ntc-chip-revived/CHIP_Pro-Hardware/v1.0/CHIP_Pro_v1_0_Stackup.pdf

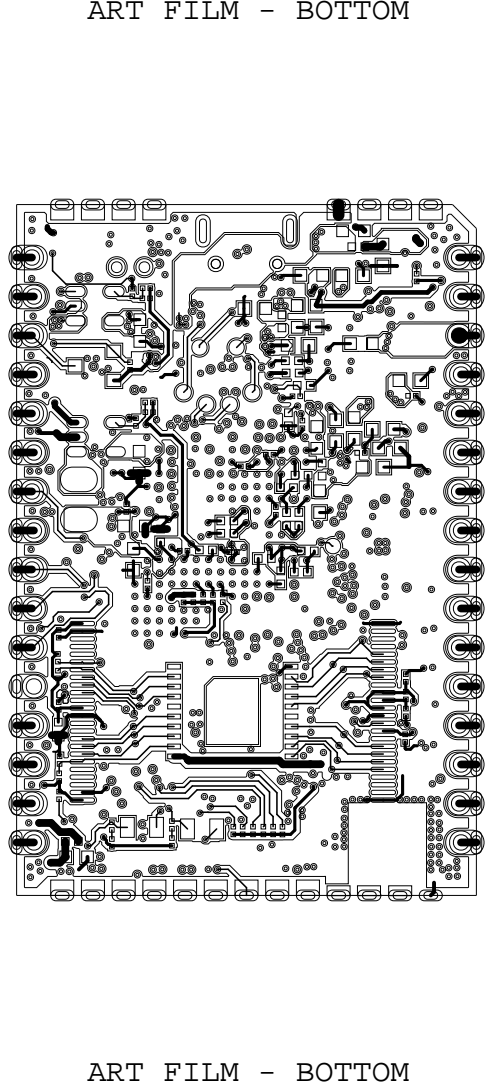
[picture p33: page 1]

ART FILM - BOTTOM

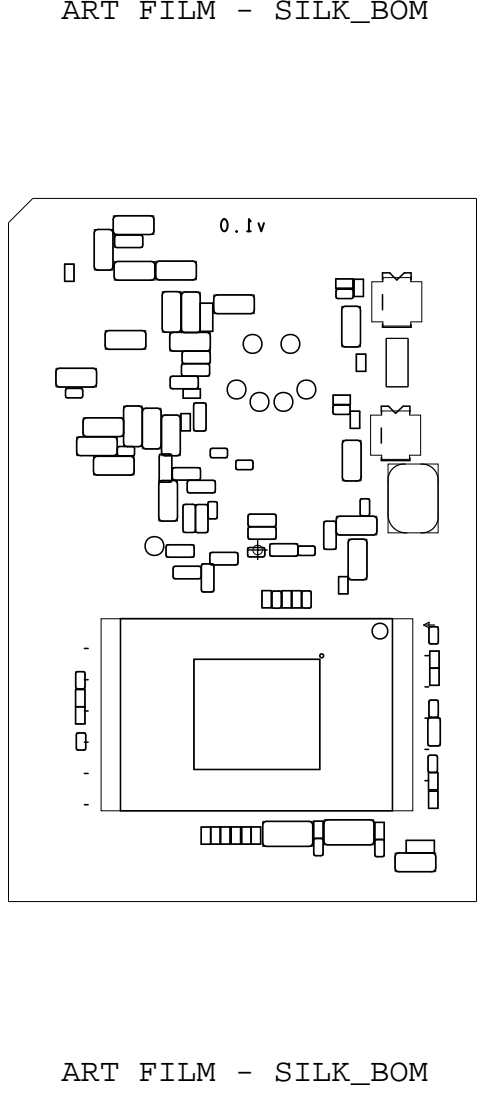
[picture p34: page 2]
ART FILM - SILK_BOM

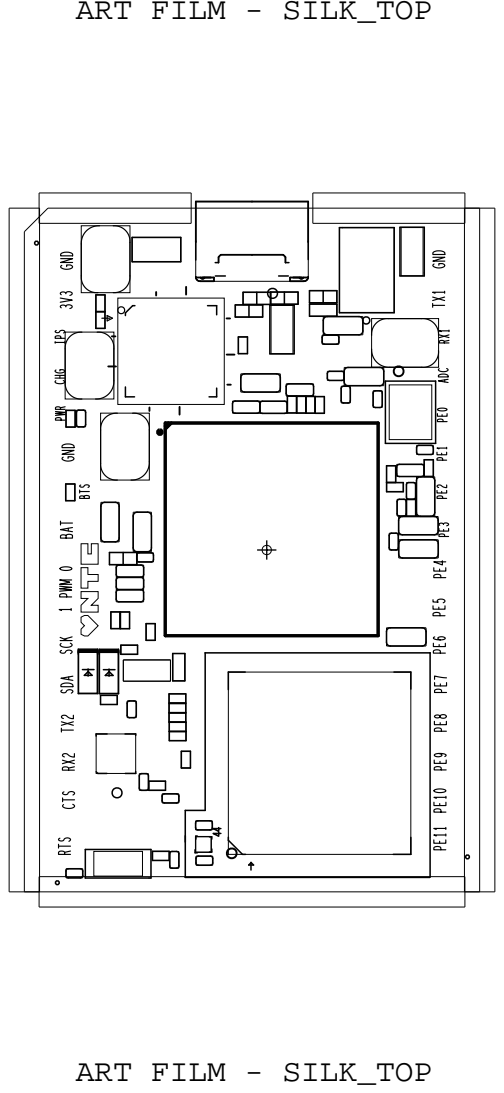
[picture p35: page 3]
ART FILM - SILK_TOP; GND TX1 ADC RX1 PE0 PE2 PE1 PE3 PE5 PE4 PE7 PE6 PE8 PE10 PE9 PE11; BTS

GND 3V3 CHG IPS PWR

GND 0 BAT 1 PWM SCK SDA TX2 CTS RX2 RTS

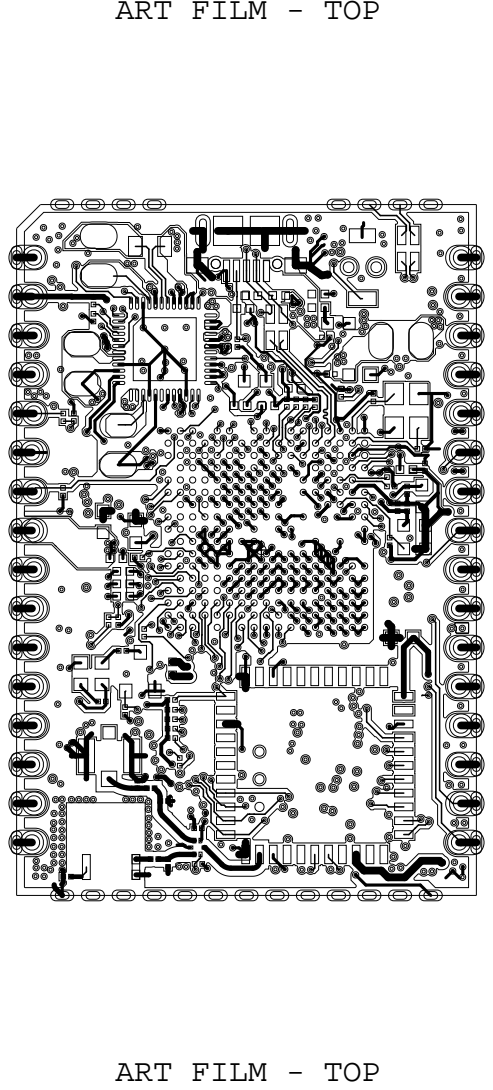
[picture p36: page 4]

ART FILM - TOP

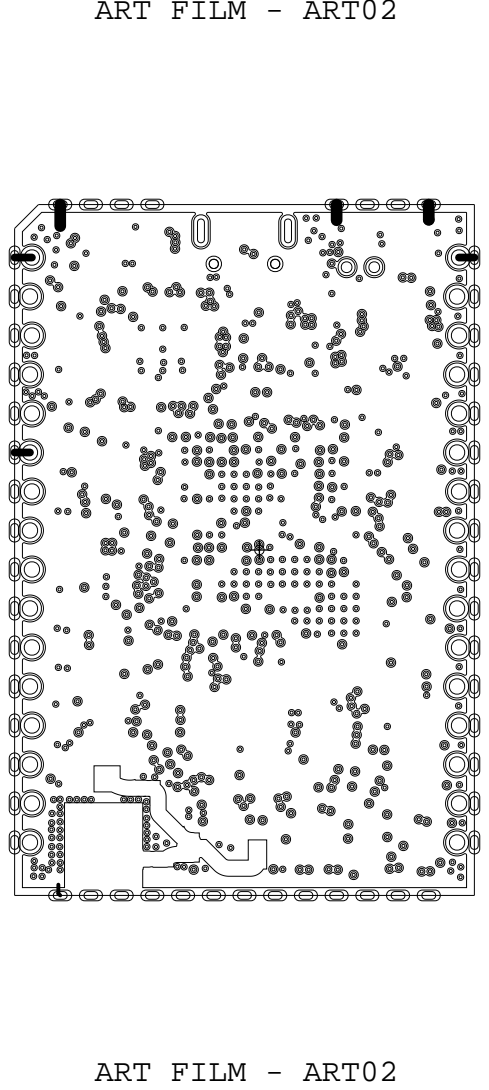
[picture p37: page 5]
ART FILM - ART02

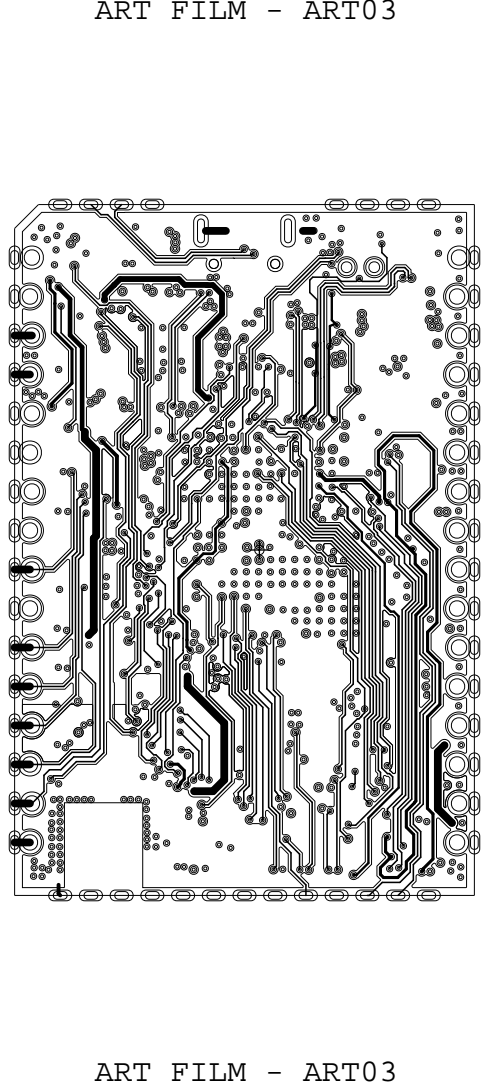
[picture p38: page 6]

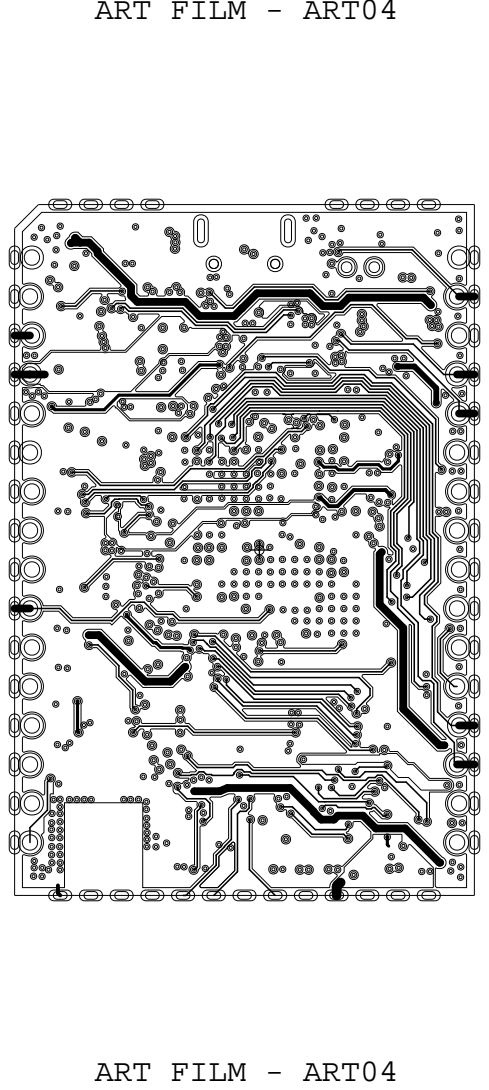
[picture p39: page 7]

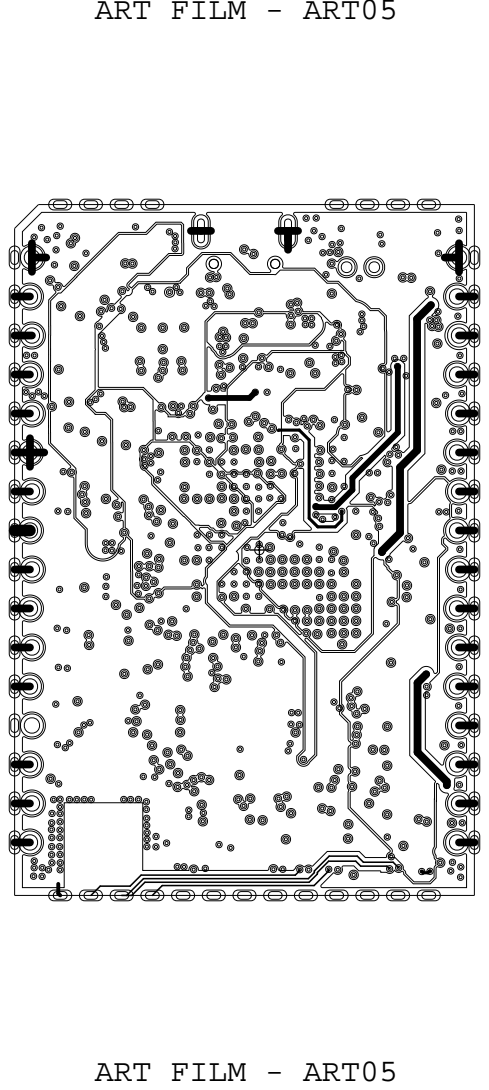
[picture p40: page 8]
