ntc-chip-revived/CHIP_Pro-Hardware/v1.0/CHIP_Pro_v1_0_PartMap.pdf

# ART FILM - ST

J5 | | J6

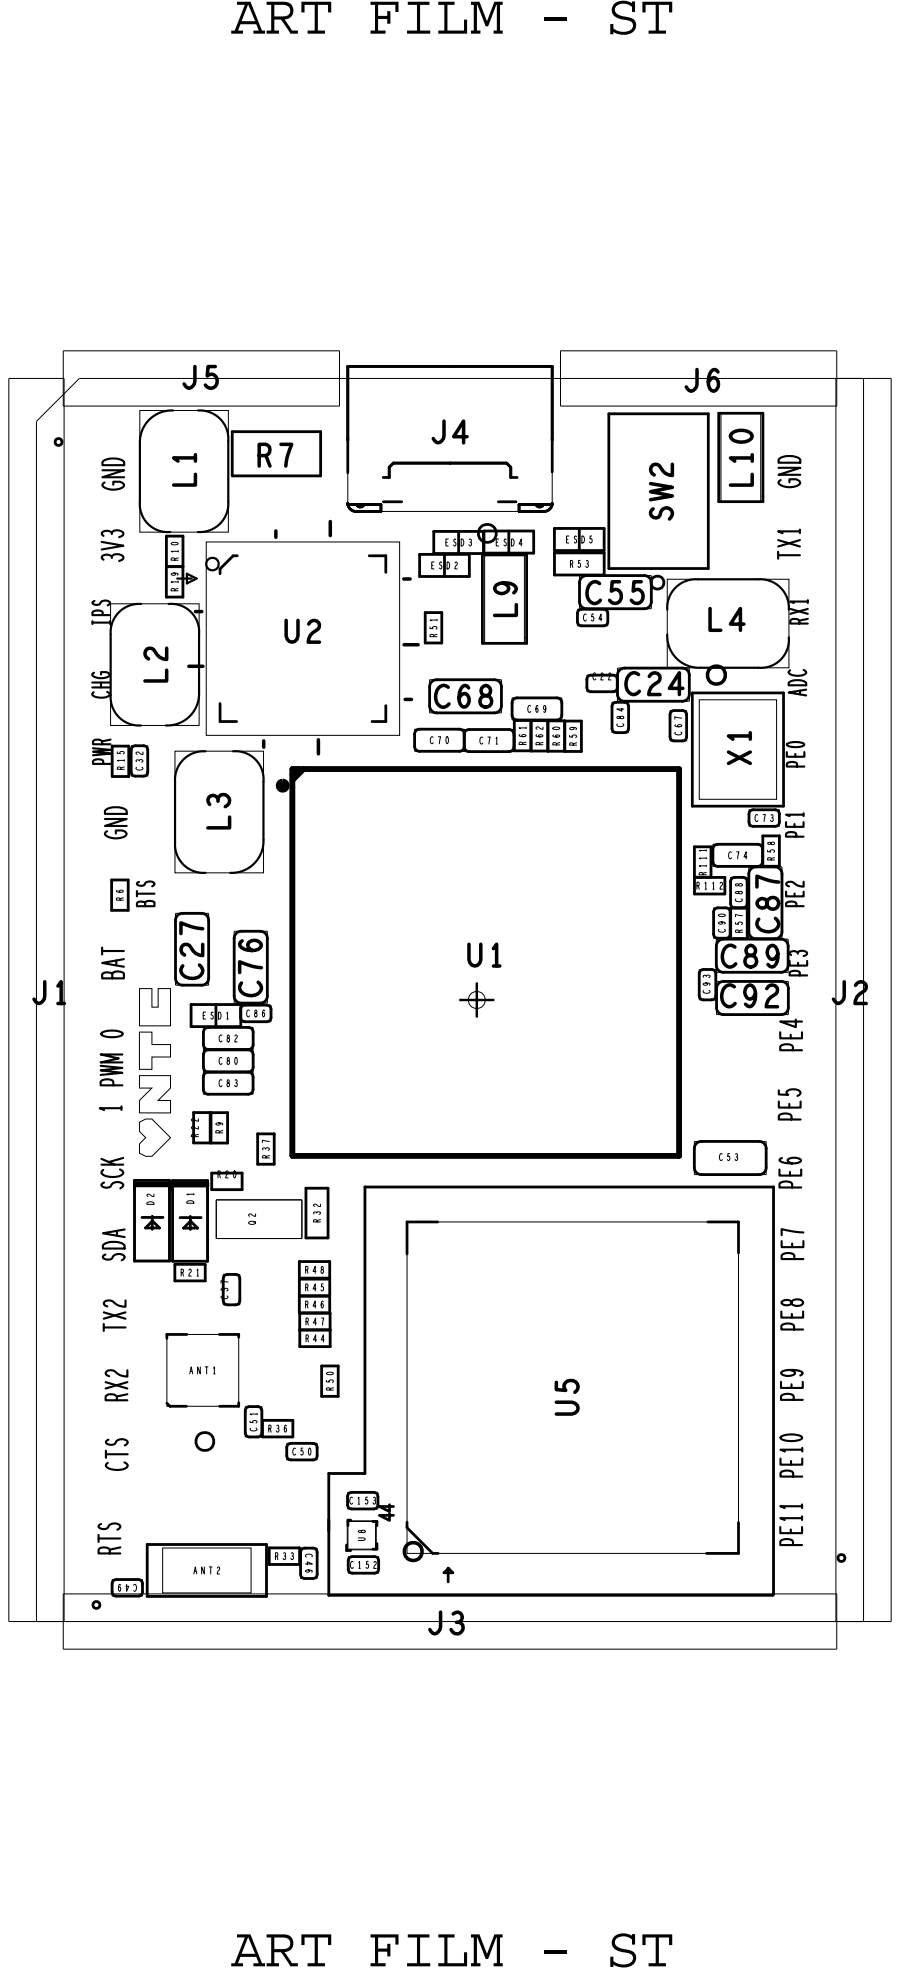
[picture p42: page 1]

# ART FILM - SB

v1.0

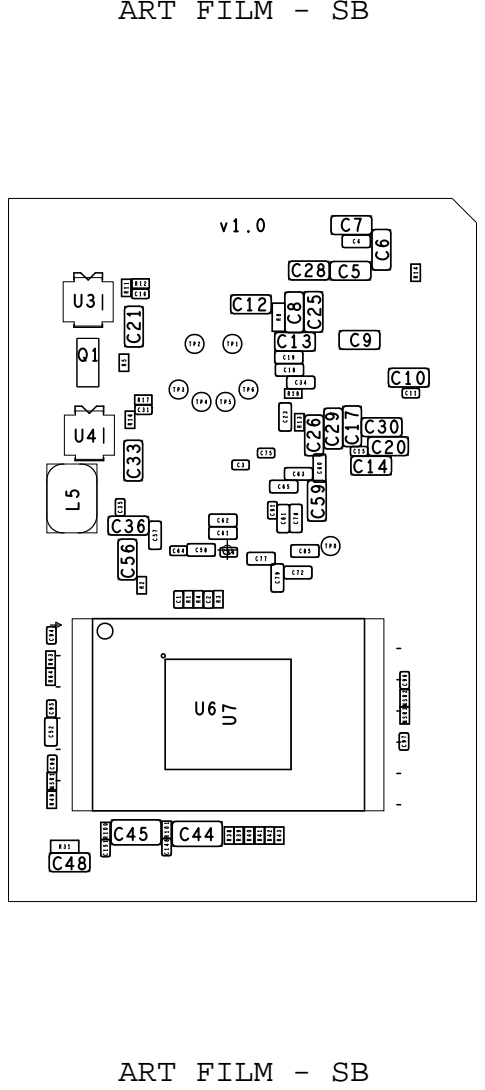
[picture p43: page 2]
