ntc-chip-revived/CHIP_Pro-Hardware/v0.9/CHIP_Pro_SCH_V0_9a.pdf

# Schematics Index：

# P01: REVISION HISTORY

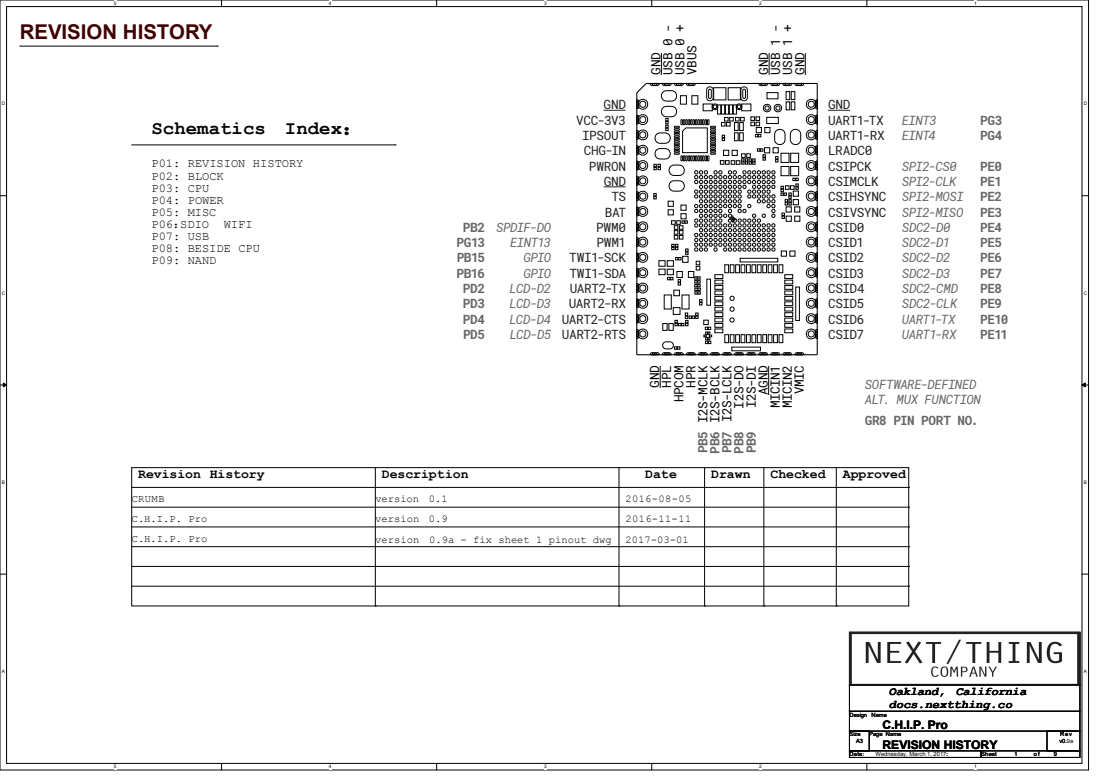
[picture p44: page 1]
Revision History; Description; Date; Drawn; Checked; Approved; P02: BLOCK P03: CPU P04: POWER P05: MISC P06：SDIO WIFI P07: USB P08: BESIDE CPU P09: NAND; REVISION HISTORY; CRUMB; version 0.1; C.H.I.P. Pro; version 0.9; Design Name; Size; Page Name; Date:; Sheet; v0.9a C.H.I.P. Pro A3; GND VCC-3V3 IPSOUT CHG-IN PWRON GND TS BAT PWM0 PWM1 TWI1-SCK TWI1-SDA UART2-TX UART2-RX UART2-CTS UART2-RTS; SPDIF-DO EINT13 GPIO GPIO LCD-D2 LCD-D3 LCD-D4 LCD-D5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

SOFTWARE-DEFINED
ALT. MUX FUNCTION
GR8 PIN PORT NO.

Oakland, California
docs.nextthing.co
C.H.I.P. Pro A3
REVISION HISTORY
Wednesday, March 1, 2017:

# BATT

# DCIN

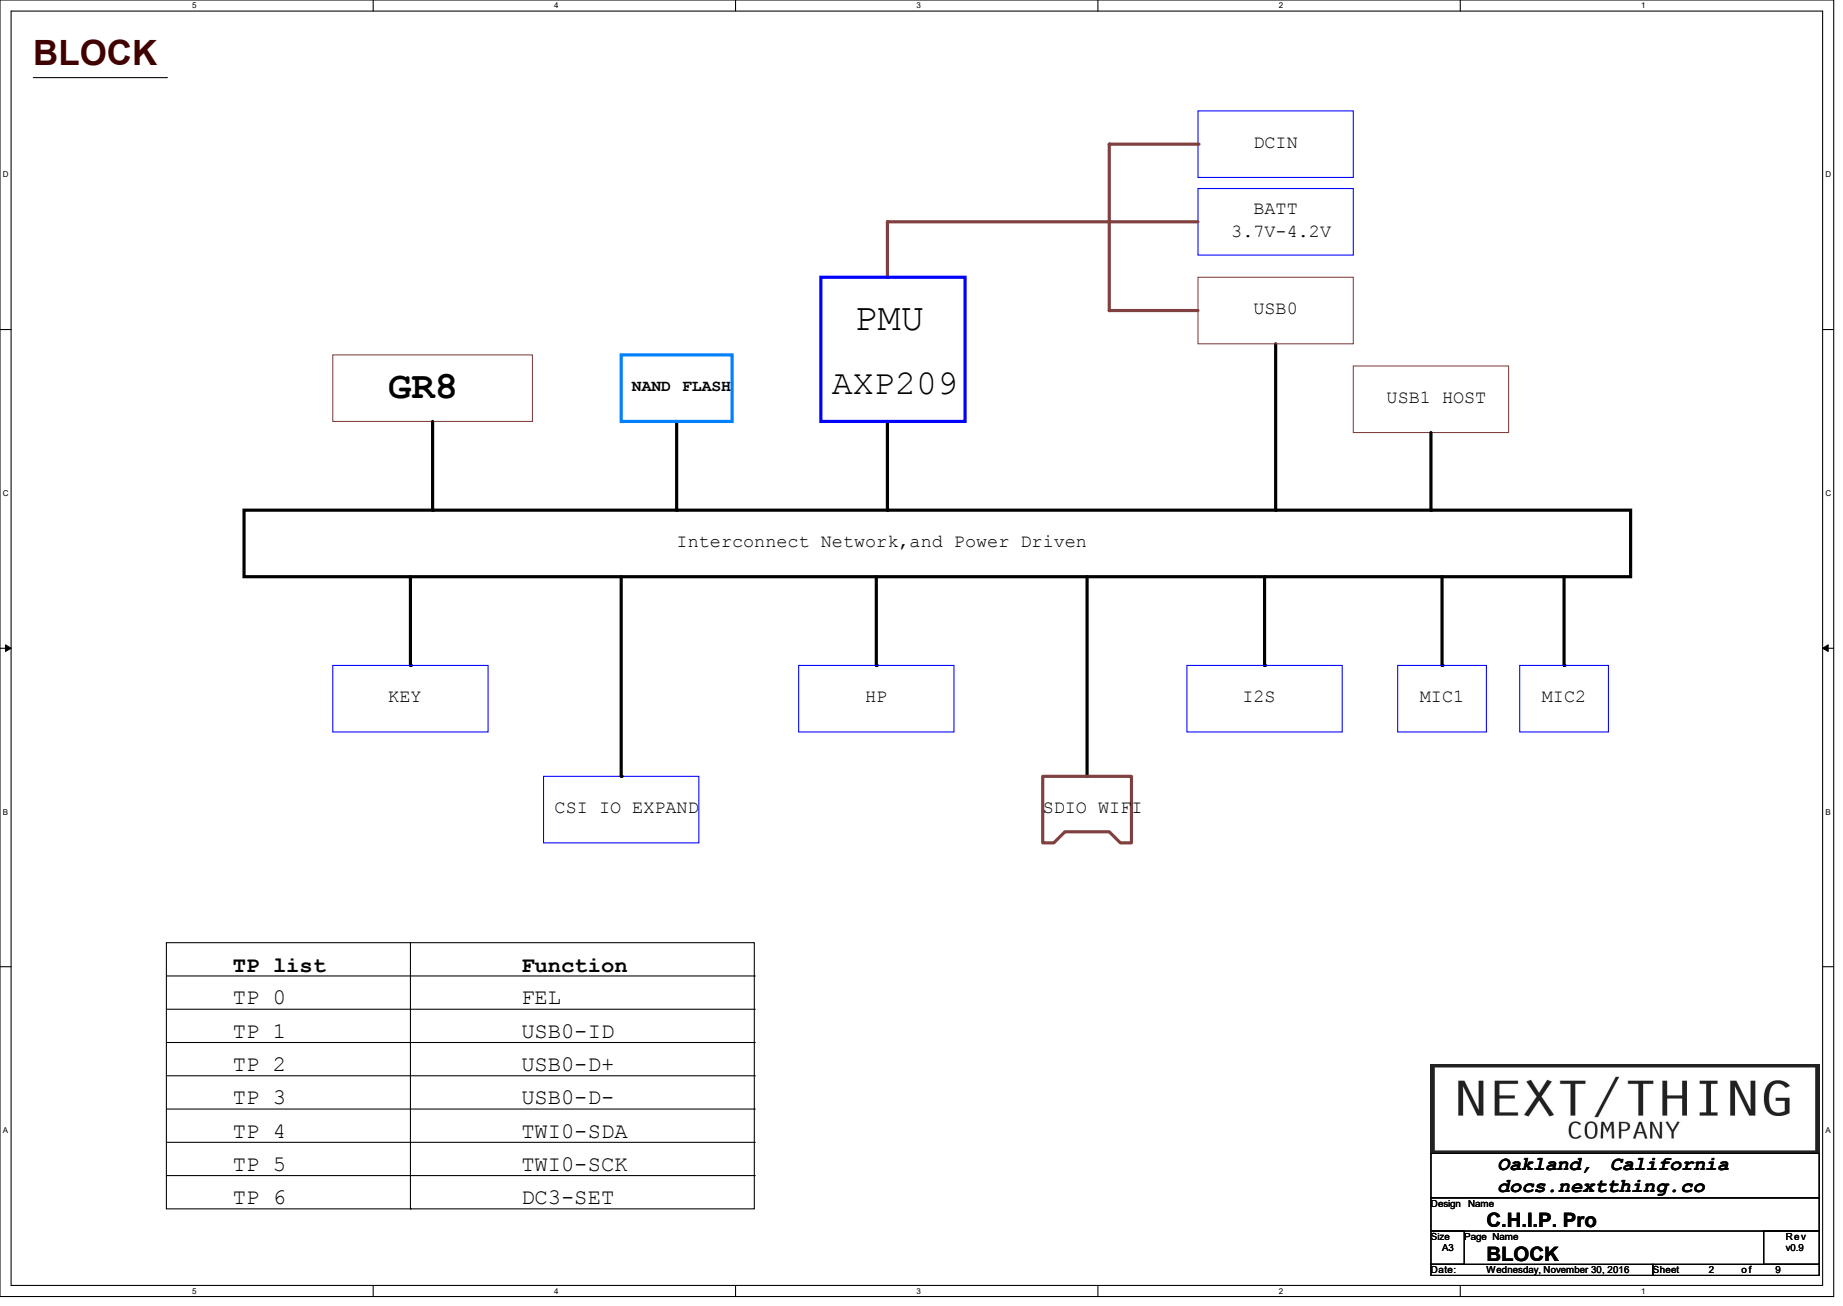
[picture p45: page 2]
SDIO WIFI; USB0; KEY; PMU; AXP209; MIC1; BLOCK; NAND FLASH GR8; USB1 HOST; MIC2; TP list; Function; FEL USB0-ID USB0-D+ USB0-D- TWI0-SDA TWI0-SCK; DC3-SET; Design Name; v0.9 C.H.I.P. Pro A3; Wednesday, November 30, 2016

Interconnect Network,and Power Driven

CSI IO EXPAND

Oakland, California
docs.nextthing.co

CPU | NAND

# SYS

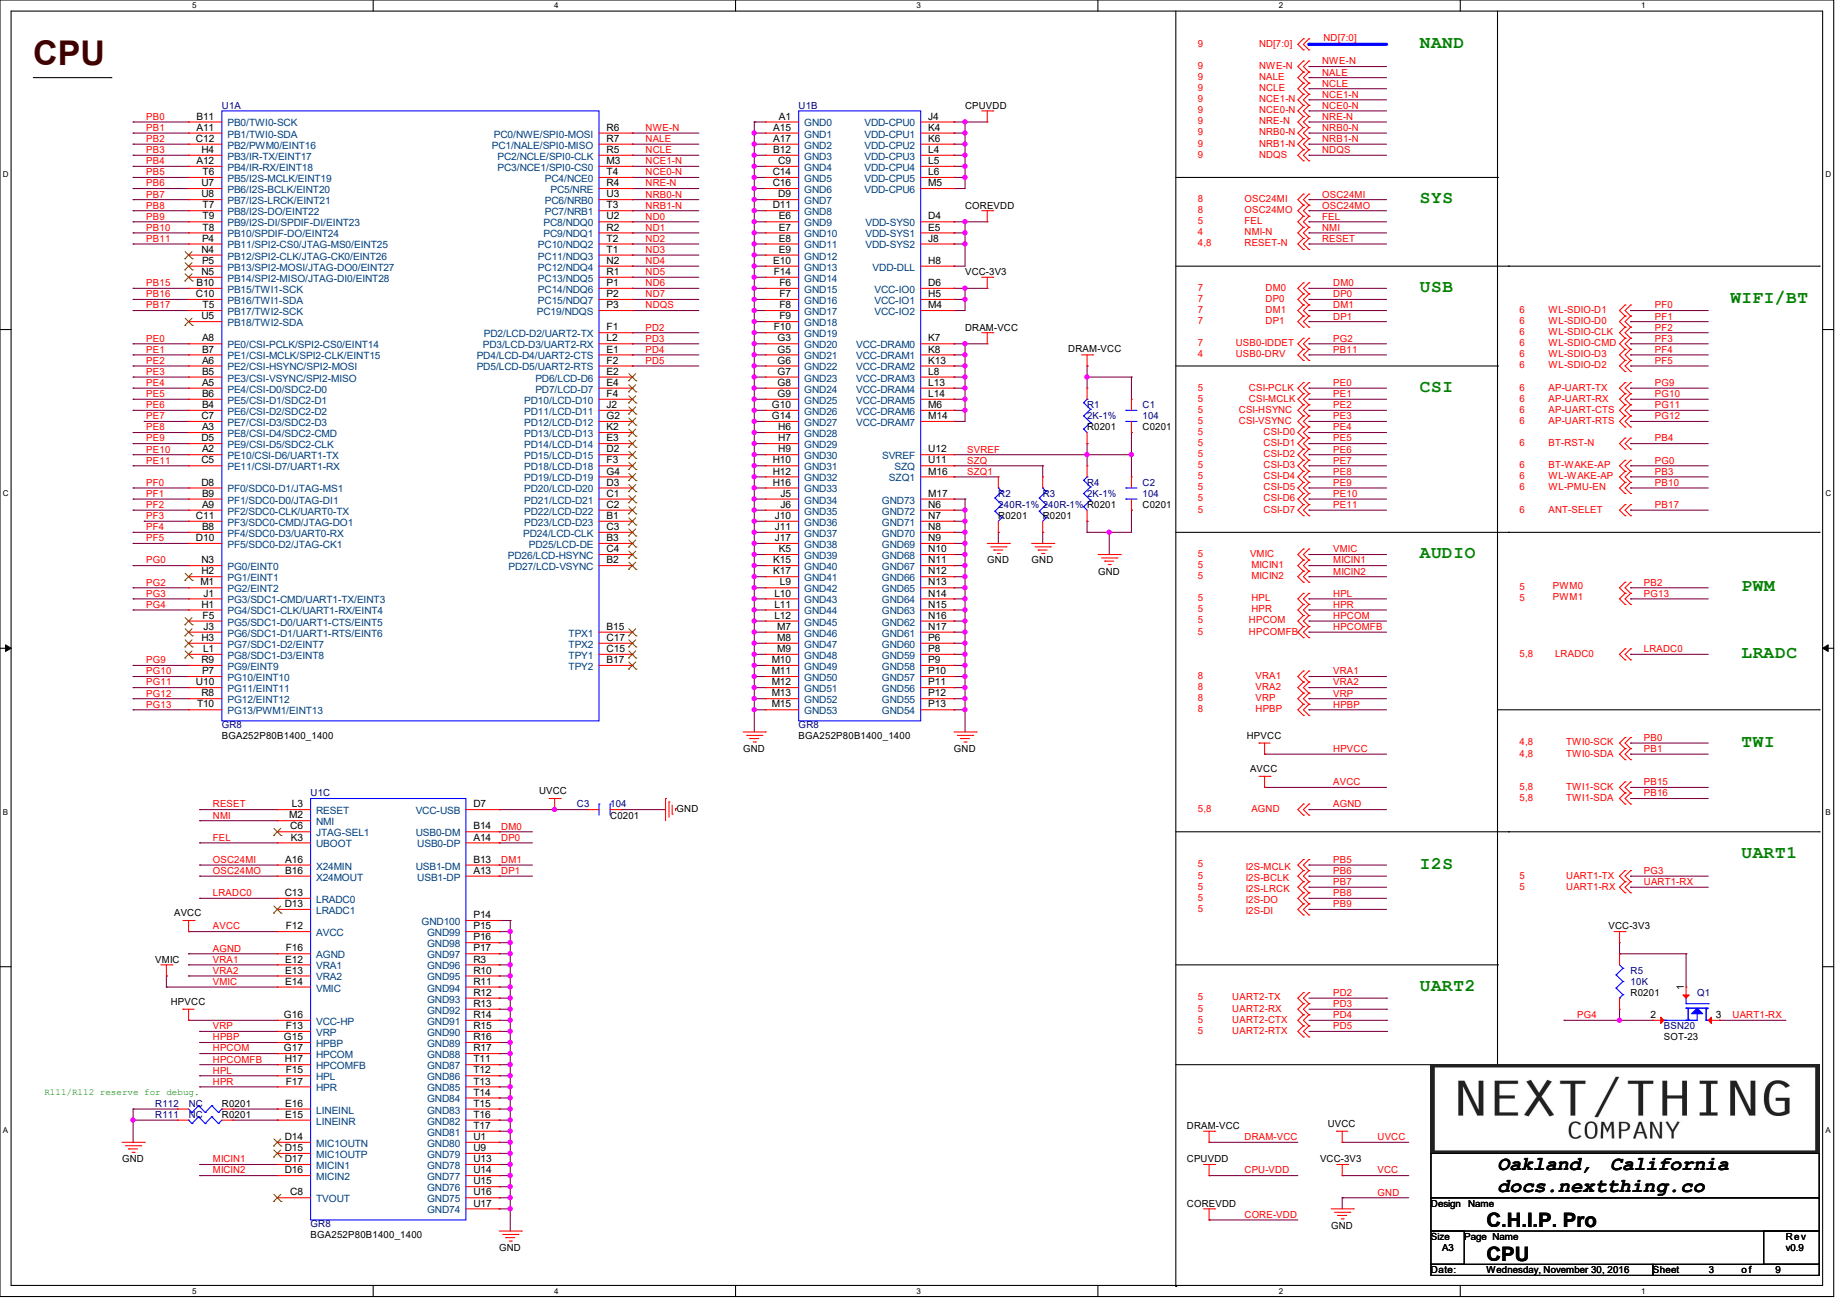
[picture p46: page 3]

VDD-CPU0 J4 VDD-CPU1 K4 VDD-CPU2 K6 VDD-CPU3 L4 VDD-CPU4 L5 VDD-CPU5 L6 VDD-CPU6 M5 VDD-DLL H8 VDD-SYS0 D4 VDD-SYS1 E5 VDD-SYS2 J8 VCC-DRAM0 K7 VCC-DRAM1 K8 VCC-DRAM2 K13 VCC-DRAM3 L8 VCC-DRAM4 L13 VCC-DRAM5 L14 VCC-DRAM6 M6 VCC-IO0 D6 VCC-IO1 H5 VCC-IO2 M4 GND25 G9 GND26 G10 GND27 G14 GND28 H6 GND29 H7 GND30 H9 GND31 H10 GND32 H12 GND33 H16
GND4 C9 GND5 C14 GND6 C16 GND7 D9 GND8 D11 GND9 E6 GND10 E7 GND11 E8 GND12 E9 GND13 E10 GND14 F14 GND15 F6 GND16 F7 GND17 F8 GND18 F9 GND44 L11 GND45 L12 GND43 L10 GND42 L9

PB0/TWI0-SCK B11 PB1/TWI0-SDA A11 PB2/PWM0/EINT16 C12 PB3/IR-TX/EINT17 H4 PB4/IR-RX/EINT18 A12 PB5/I2S-MCLK/EINT19 T6 PB6/I2S-BCLK/EINT20 U7 PB7/I2S-LRCK/EINT21 U8 PB8/I2S-DO/EINT22 T7 PB9/I2S-DI/SPDIF-DI/EINT23 T9 PB10/SPDIF-DO/EINT24 T8 PB11/SPI2-CS0/JTAG-MS0/EINT25 P4 PB12/SPI2-CLK/JTAG-CK0/EINT26 N4 PB13/SPI2-MOSI/JTAG-DO0/EINT27 P5 PB14/SPI2-MISO/JTAG-DI0/EINT28 N5 PB15/TWI1-SCK B10 PB16/TWI1-SDA C10 PB17/TWI2-SCK T5 PB18/TWI2-SDA U5 PE0/CSI-PCLK/SPI2-CS0/EINT14 A8 PE1/CSI-MCLK/SPI2-CLK/EINT15 B7 PE2/CSI-HSYNC/SPI2-MOSI A6 PE3/CSI-VSYNC/SPI2-MISO B5 PE4/CSI-D0/SDC2-D0 A5 PE5/CSI-D1/SDC2-D1 B6 PE6/CSI-D2/SDC2-D2 B4 PE7/CSI-D3/SDC2-D3 C7 PE8/CSI-D4/SDC2-CMD A3 PE9/CSI-D5/SDC2-CLK D5 PE10/CSI-D6/UART1-TX A2 PE11/CSI-D7/UART1-RX C5 PF0/SDC0-D1/JTAG-MS1 D8 PF1/SDC0-D0/JTAG-DI1 B9 PF2/SDC0-CLK/UART0-TX A9 PF3/SDC0-CMD/JTAG-DO1 C11 PF4/SDC0-D3/UART0-RX B8 PF5/SDC0-D2/JTAG-CK1 D10 PG0/EINT0 N3 PG1/EINT1 H2 PG2/EINT2 M1 PG3/SDC1-CMD/UART1-TX/EINT3 J1 PG4/SDC1-CLK/UART1-RX/EINT4 H1 PG5/SDC1-D0/UART1-CTS/EINT5 F5 PG6/SDC1-D1/UART1-RTS/EINT6 J3 PG7/SDC1-D2/EINT7 H3 PG8/SDC1-D3/EINT8 L1 PG9/EINT9 R9 PG10/EINT10 P7 PG11/EINT11 U10 PG12/EINT12 R8 PG13/PWM1/EINT13 T10

PC1/NALE/SPI0-MISO R7 PC0/NWE/SPI0-MOSI R6 PC3/NCE1/SPI0-CS0 M3 PC2/NCLE/SPI0-CLK R5 PC5/NRE R4 PC6/NRB0 U3 PC8/NDQ0 U2 PC10/NDQ2 T2 PC11/NDQ3 T1 PC13/NDQ5 R1 PC12/NDQ4 N2 PC19/NDQS P3 PC14/NDQ6 P1 PC9/NDQ1 R2 PC7/NRB1 T3 PC4/NCE0 T4 PC15/NDQ7 P2

PD2/LCD-D2/UART2-TX F1 PD3/LCD-D3/UART2-RX L2 PD4/LCD-D4/UART2-CTS E1 PD5/LCD-D5/UART2-RTS F2 PD6/LCD-D6 E2 PD7/LCD-D7 E4 PD10/LCD-D10 F4 PD11/LCD-D11 J2 PD12/LCD-D12 G2 PD13/LCD-D13 K2 PD14/LCD-D14 E3 PD15/LCD-D15 D2 PD18/LCD-D18 F3 PD19/LCD-D19 G4 PD20/LCD-D20 D3 PD21/LCD-D21 C1 PD22/LCD-D22 C2 PD23/LCD-D23 B1 PD24/LCD-CLK C3 PD25/LCD-DE B3 PD26/LCD-HSYNC C4 PD27/LCD-VSYNC B2

HPBP HPL NMI RESET OSC24MI OSC24MO

VCC-USB D7 USB0-DM B14 USB0-DP A14 USB1-DM B13 USB1-DP A13 HPBP G15

# POWER/PMU

# VCC-1V8 AVCC

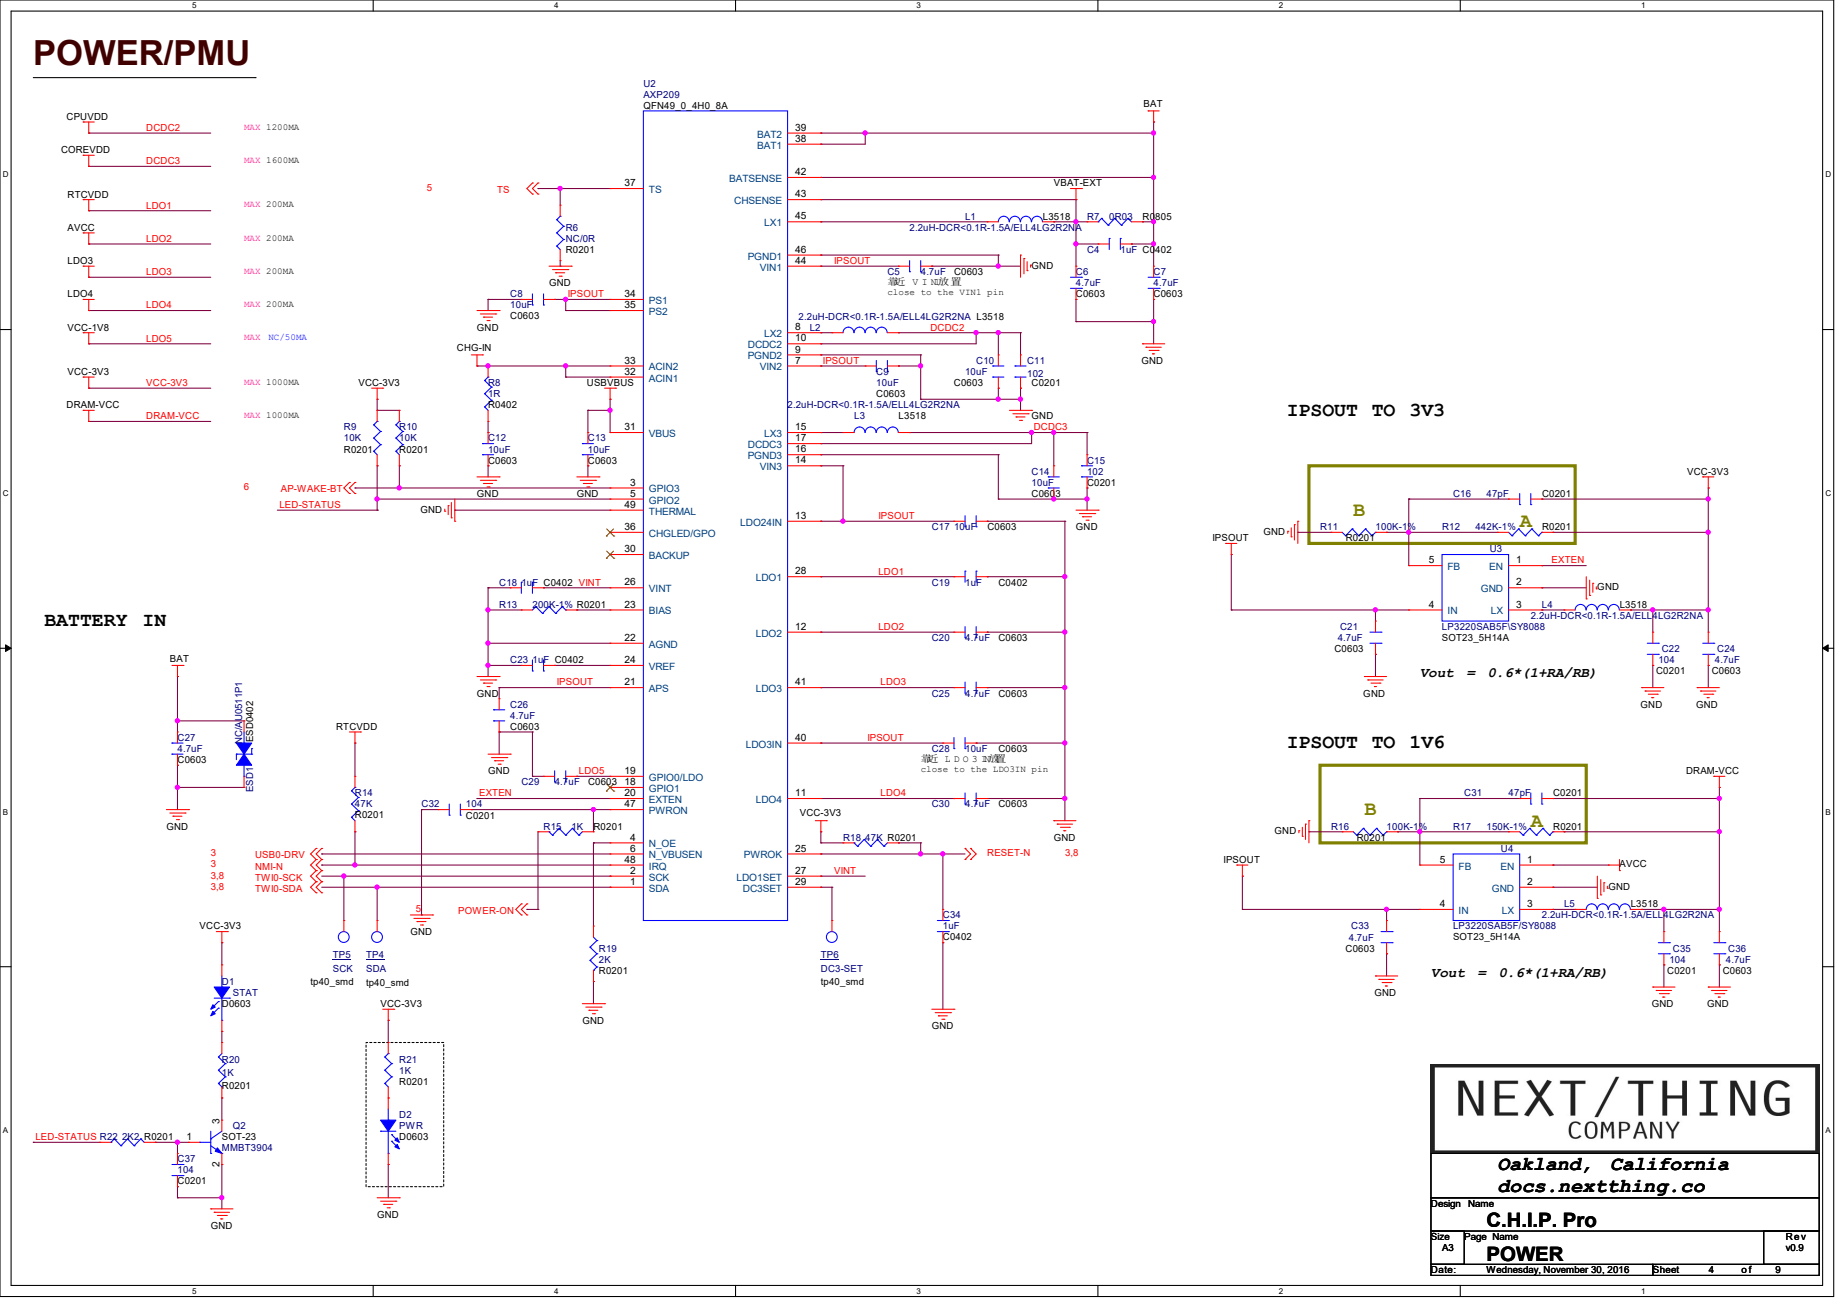
[picture p47: page 4]

BATSENSE 42 CHSENSE 43 VIN1 44
BACKUP 30 VBUS 31 ACIN1 32 ACIN2 33 PS1 34 PS2 35 CHGLED/GPO 36

close to the VIN1 pin

靠近 L D O 3 IN放置
close to the LDO3IN pin

# MISC

# PWM0 TSUART2-RTX UART2-TX

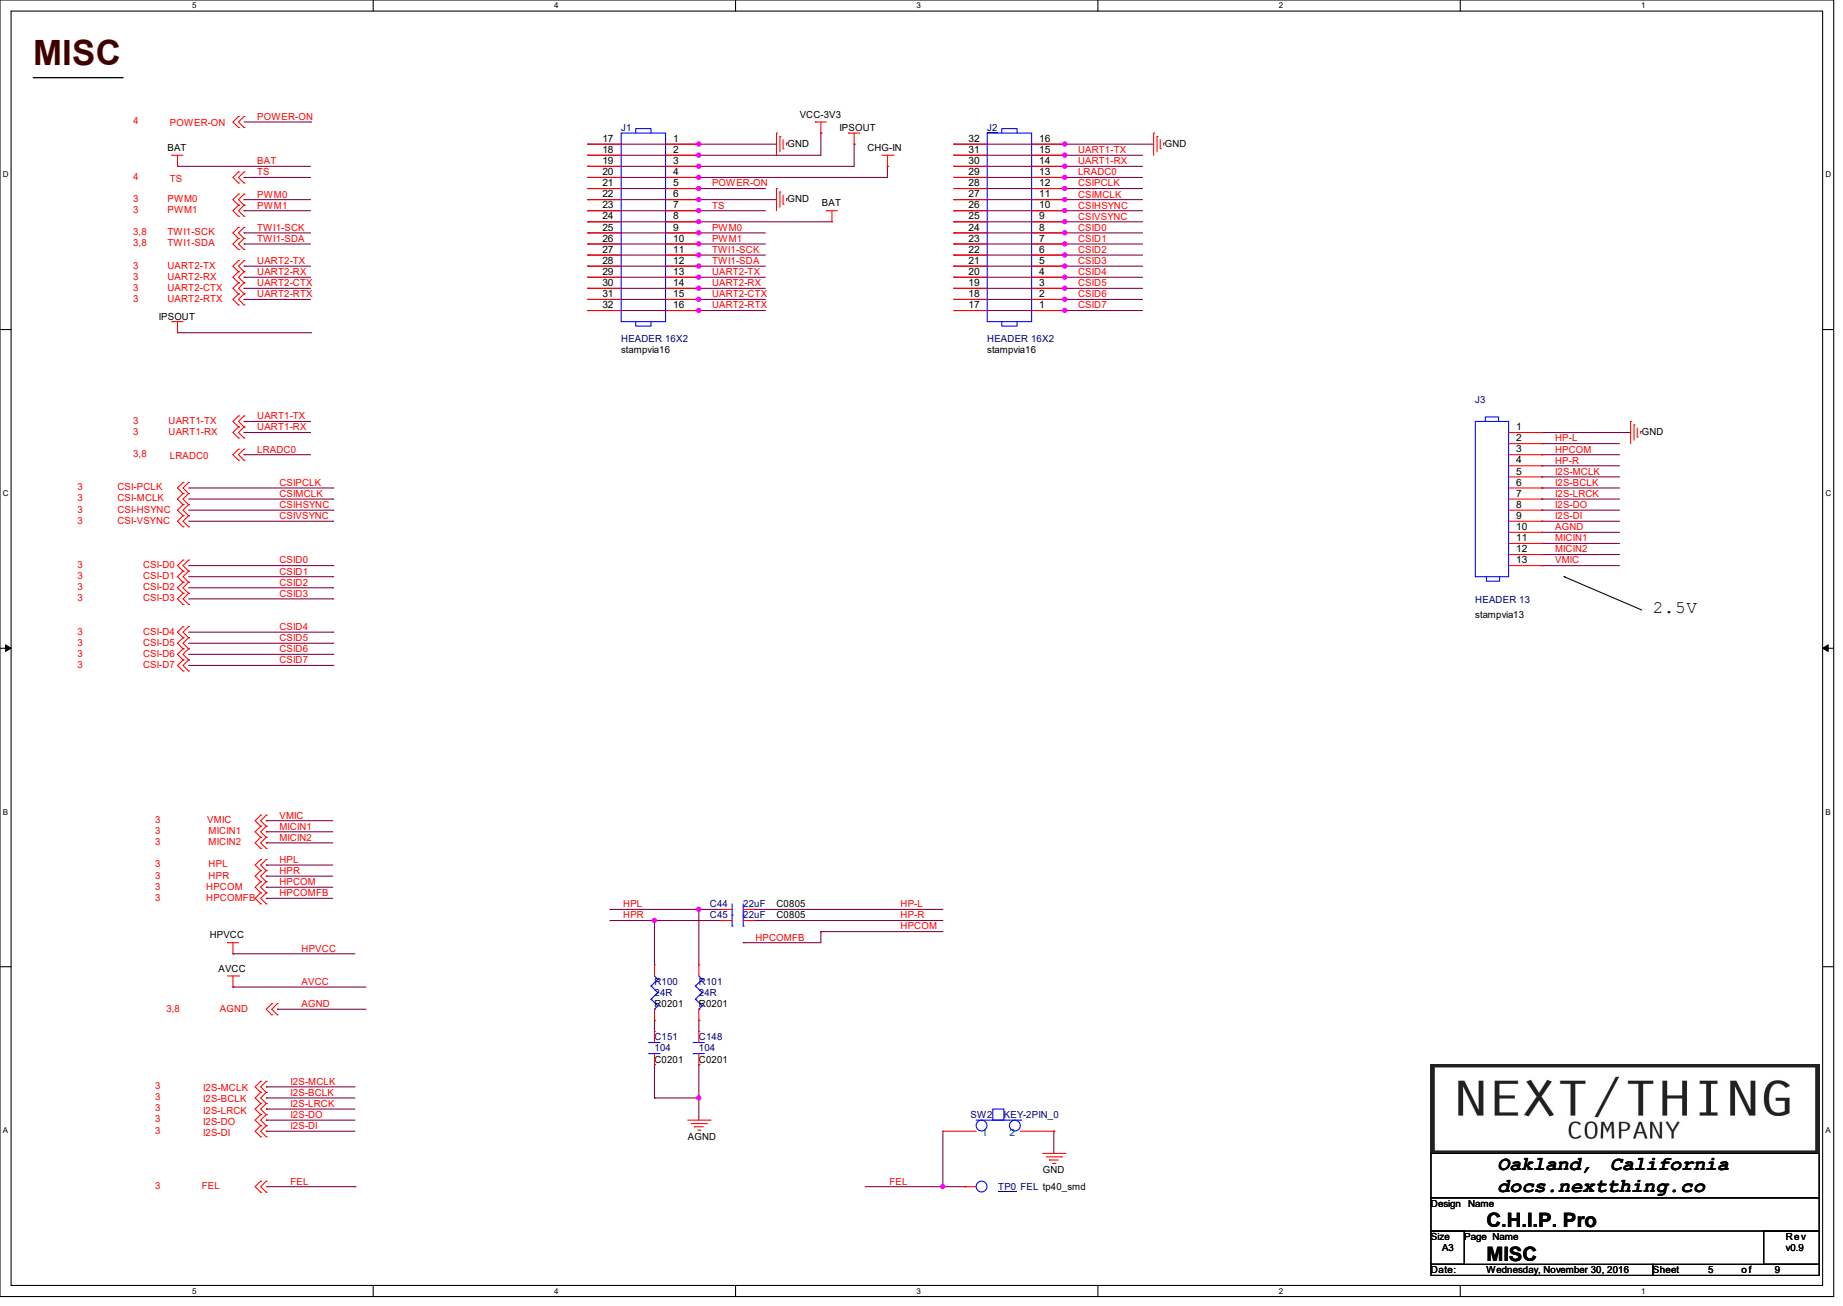
[picture p48: page 5]

IPSOUT GND BAT GND

TWI1-SCK
TWI1-SDA UART2-RTX UART2-CTX UART2-RX UART2-TX

A

B

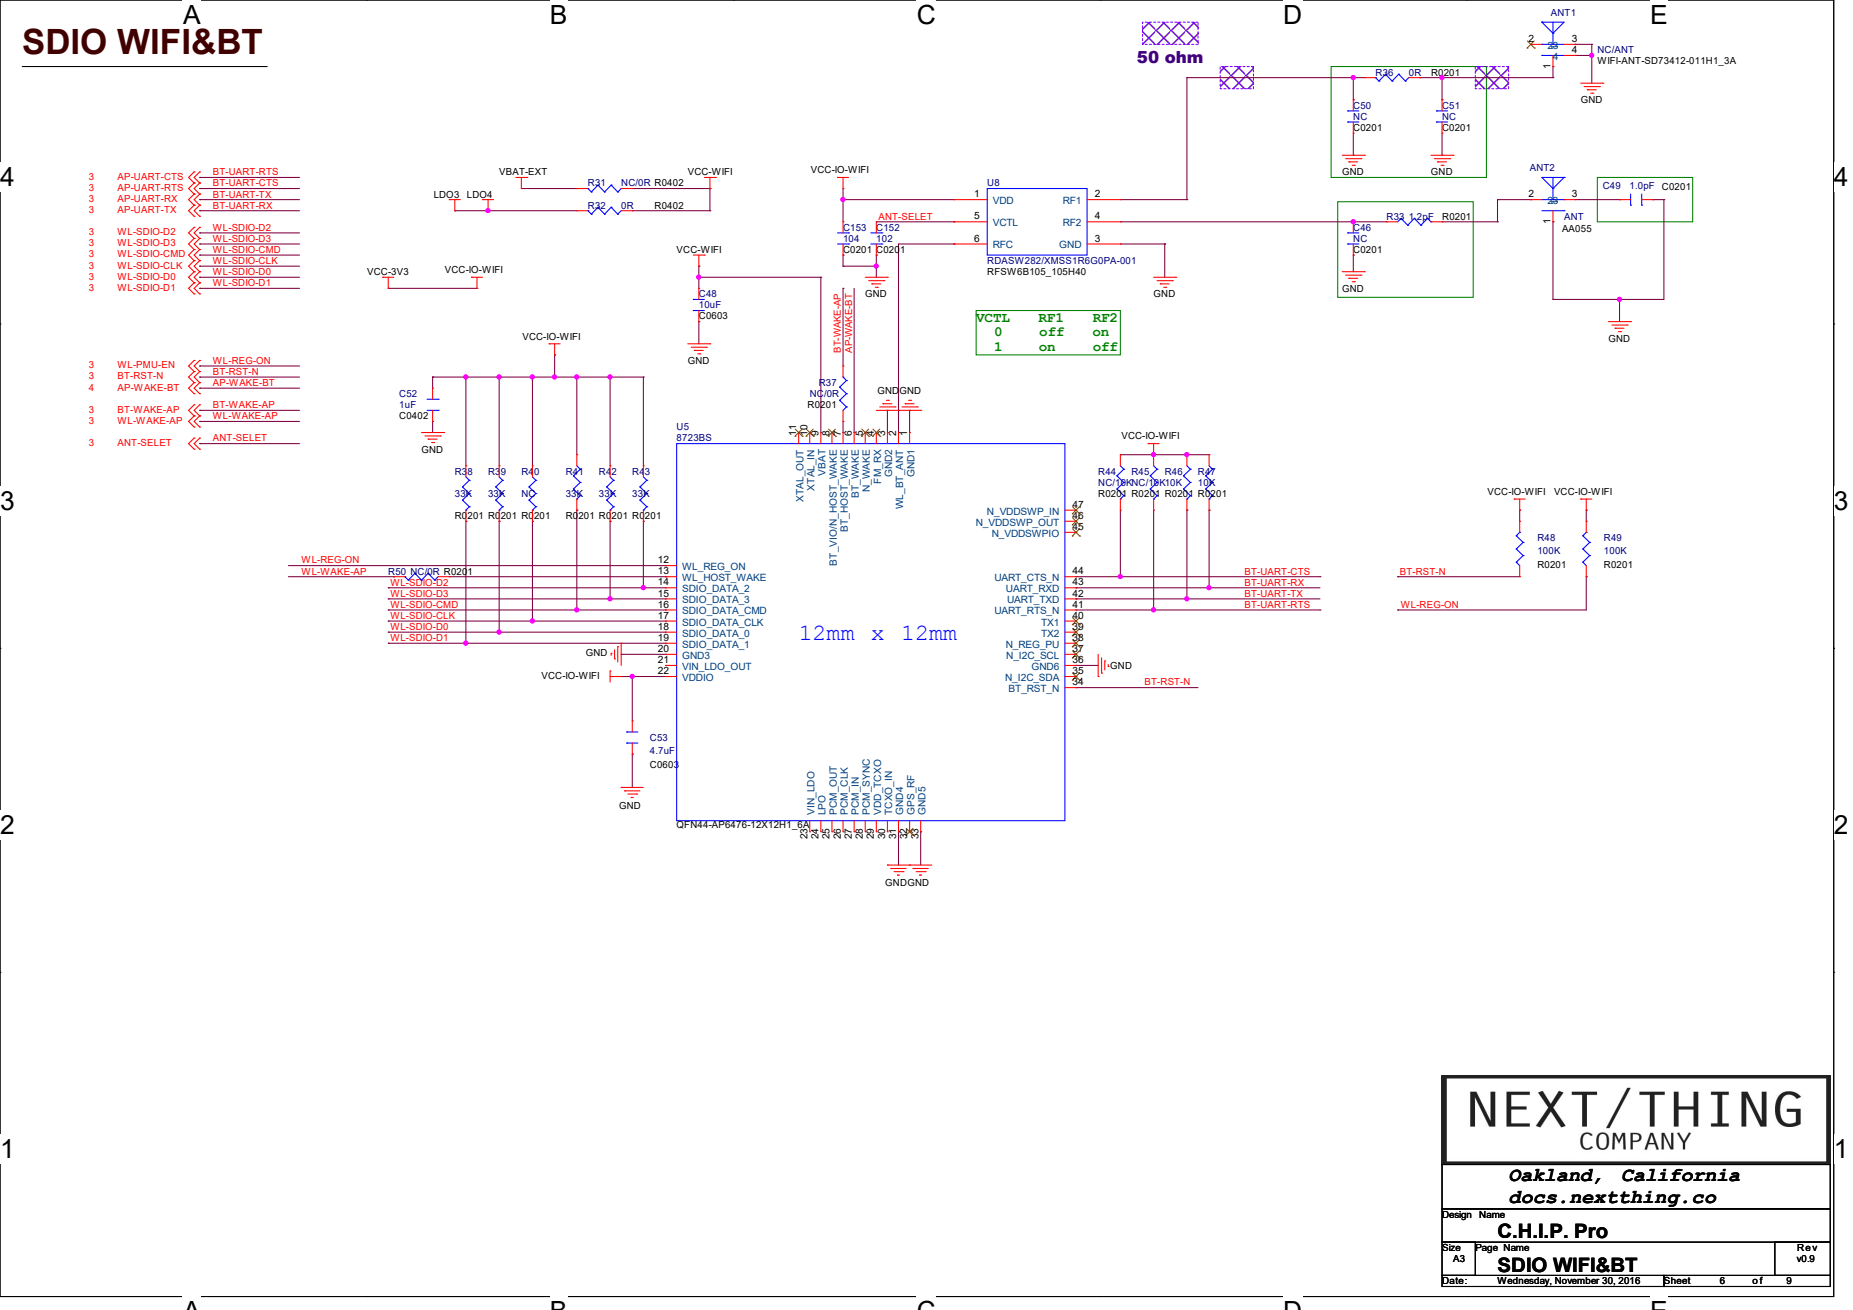
[picture p49: page 6]

BT-UART-RTS
BT-UART-CTS
BT-UART-TX
AP-WAKE-BT BT-RST-N WL-SDIO-D2 WL-SDIO-D3 WL-SDIO-CMD WL-SDIO-CLK WL-SDIO-D0 WL-SDIO-D1 BT-UART-RX

BT-RST-N WL-REG-ON WL-REG-ON

BT-RST-N WL-SDIO-CLK

# USB

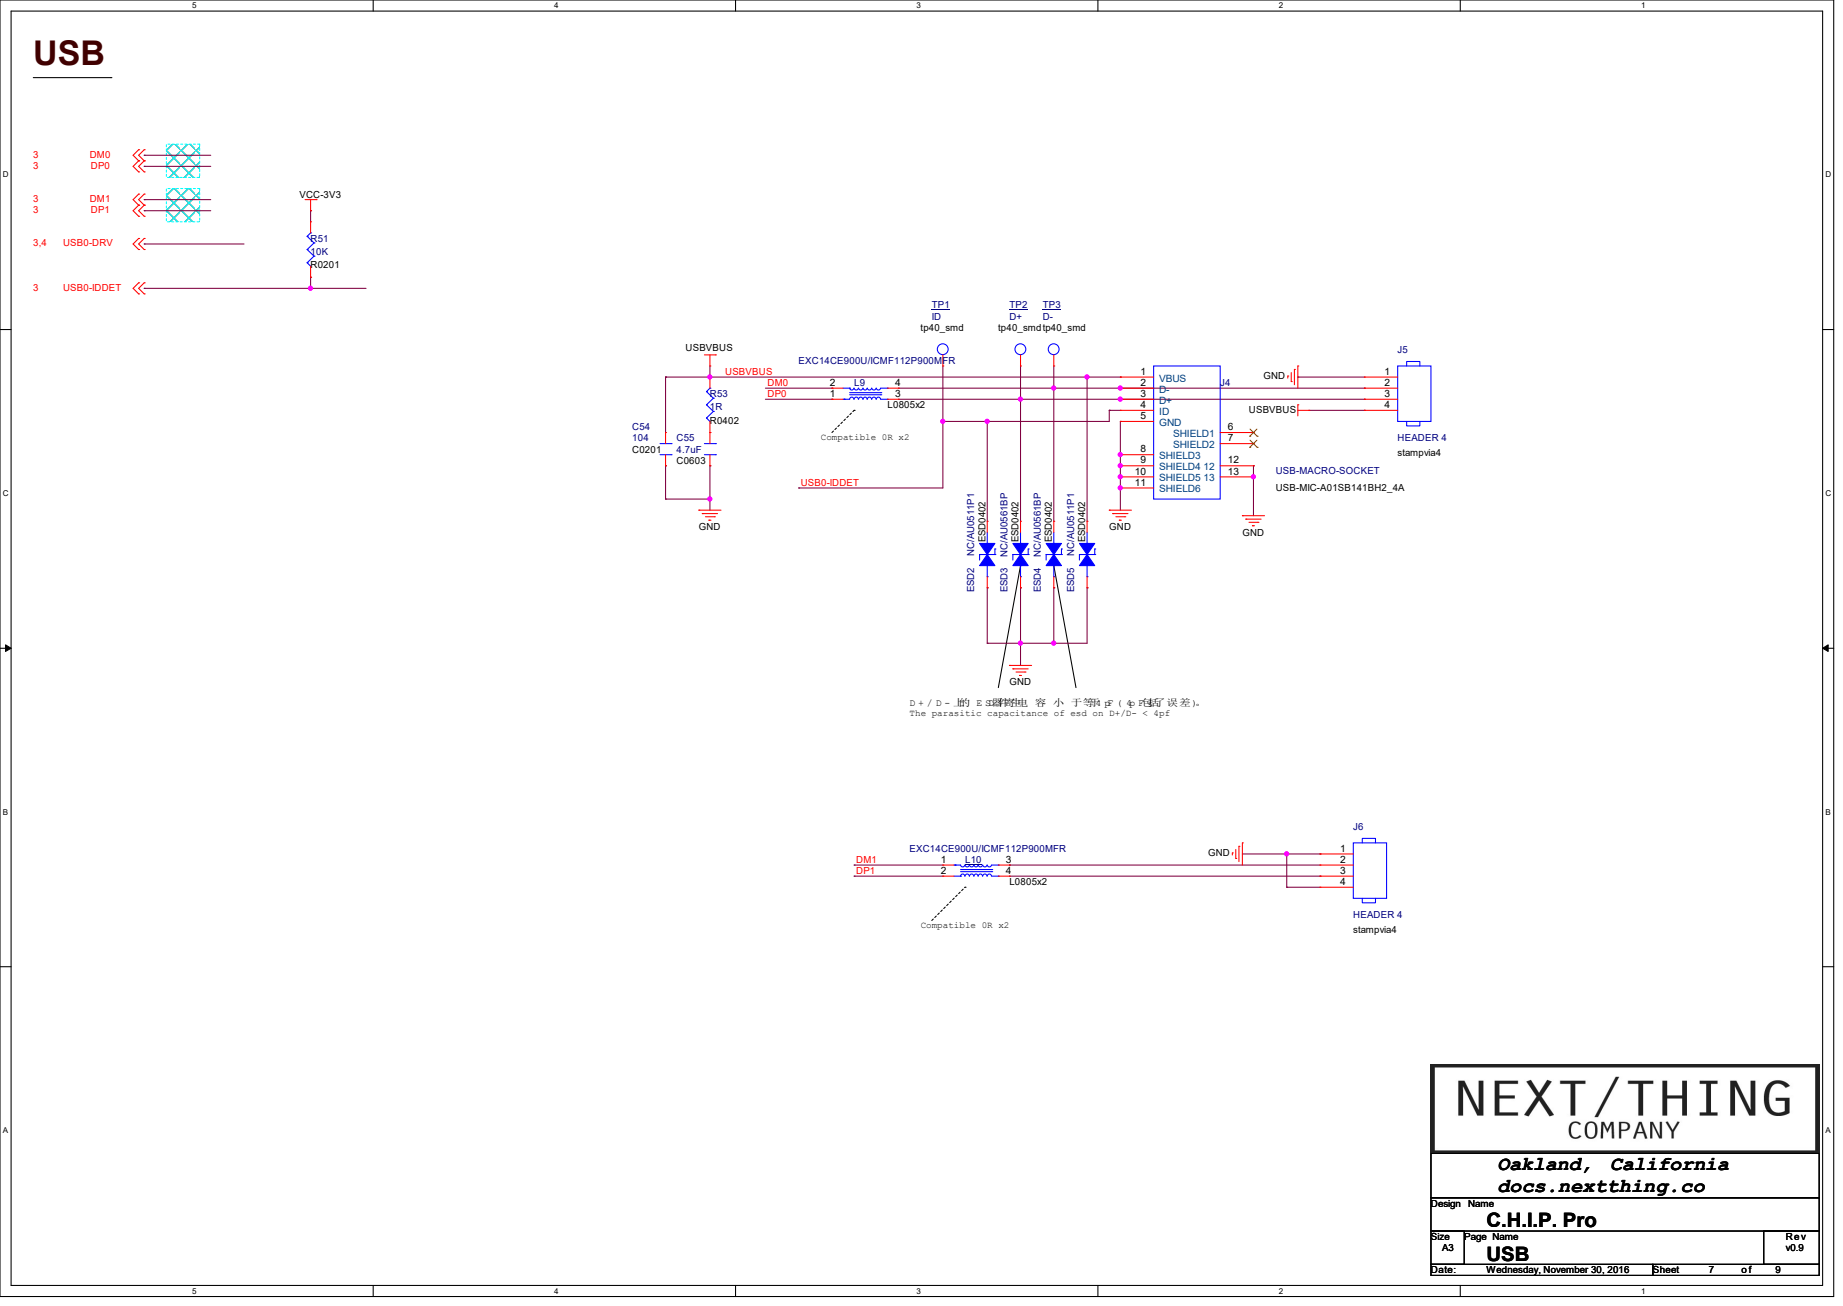
[picture p50: page 7]

4 ESD⁴ NC/AU⁰⁵⁶¹BP ESD⁰⁴⁰² TP2 D+

4 ESD³ NC/AU⁰⁵⁶¹BP ESD⁰⁴⁰²

D + / D - 上的 E SD器件寄生电 容 小 于等于4 pF ( 4p F包括了误差)。
The parasitic capacitance of esd on D+/D- < 4pf

# DRAM

# PIO-INTFACE

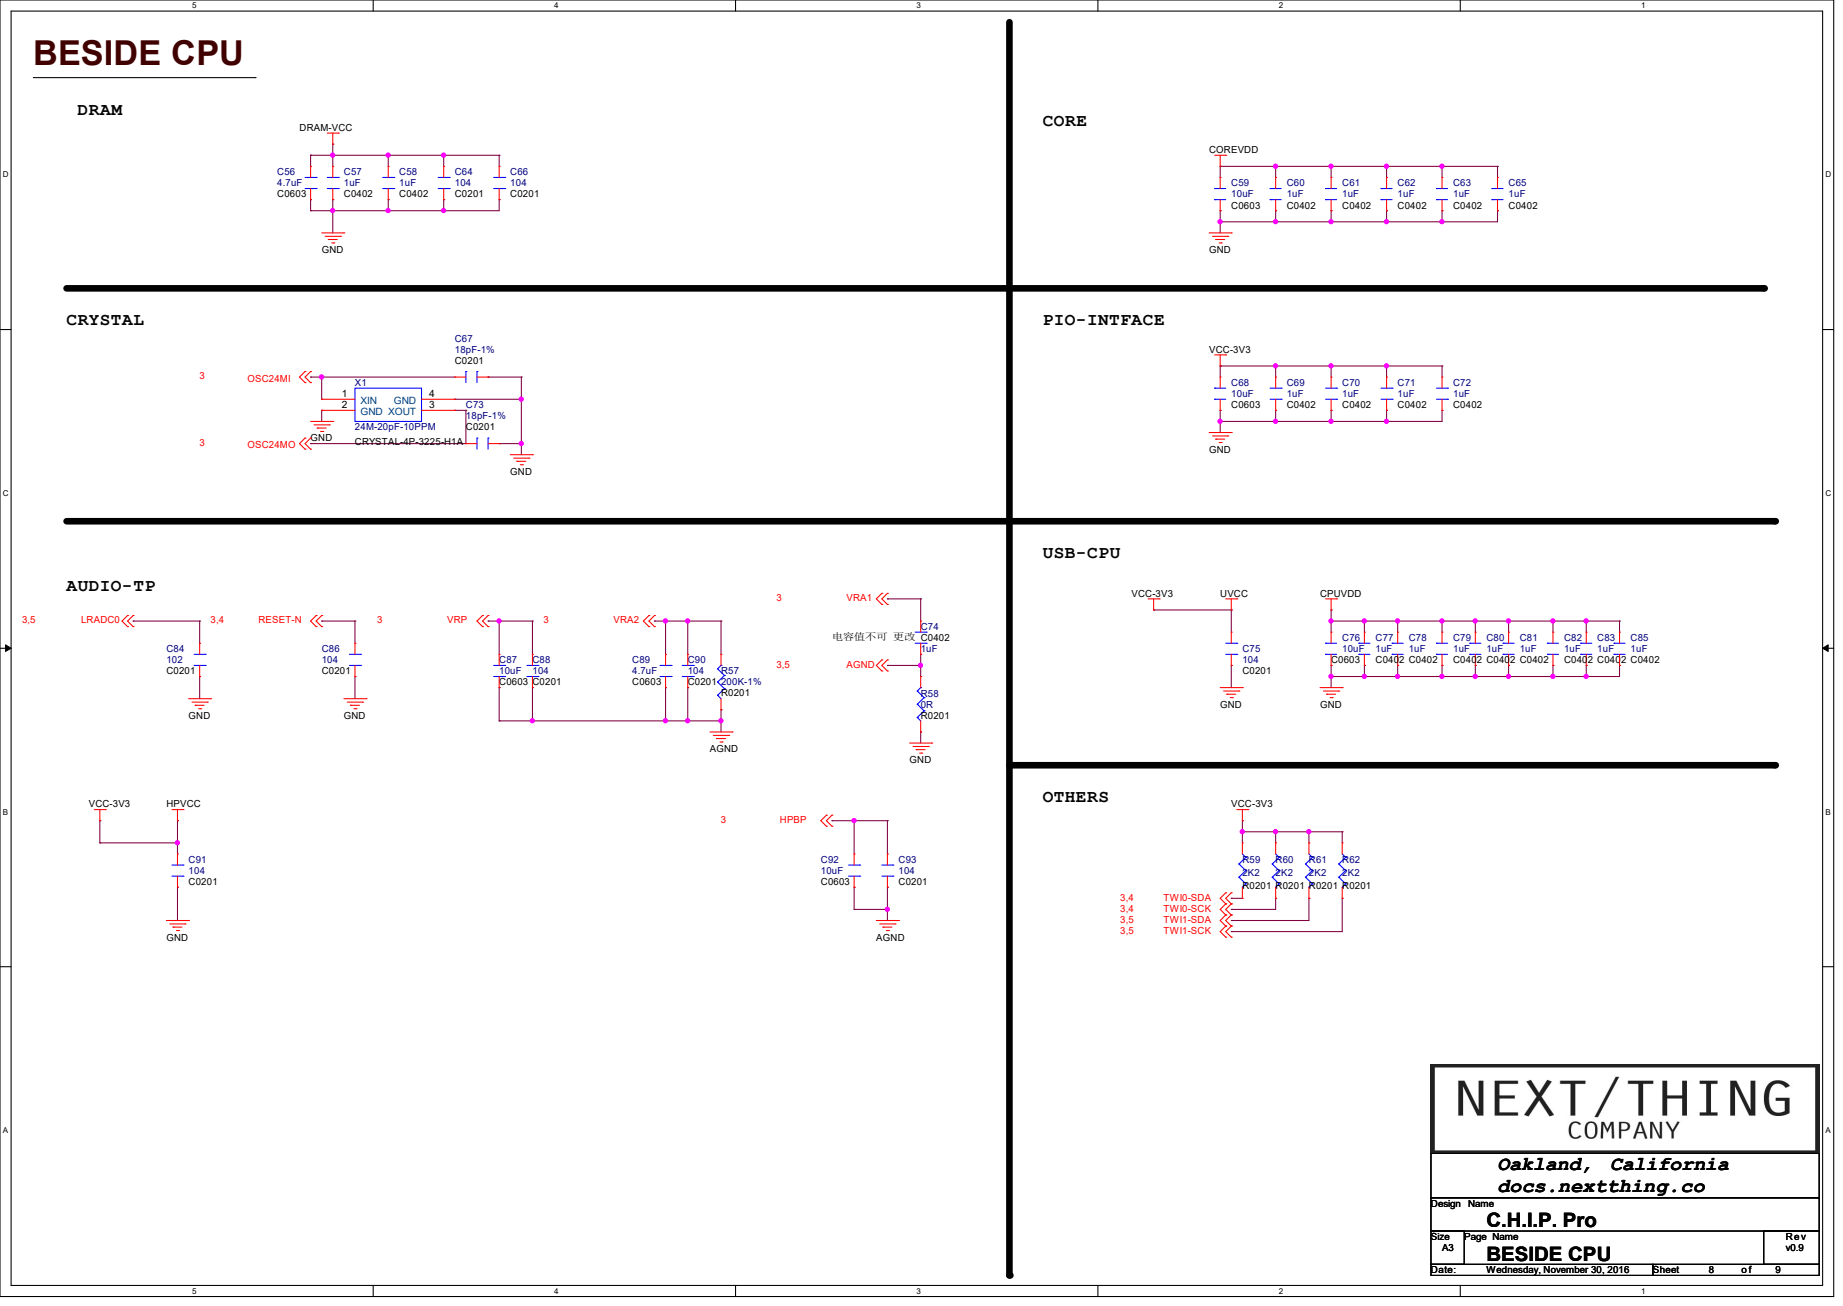
[picture p51: page 8]

# NAND

# NALE NRB1-N

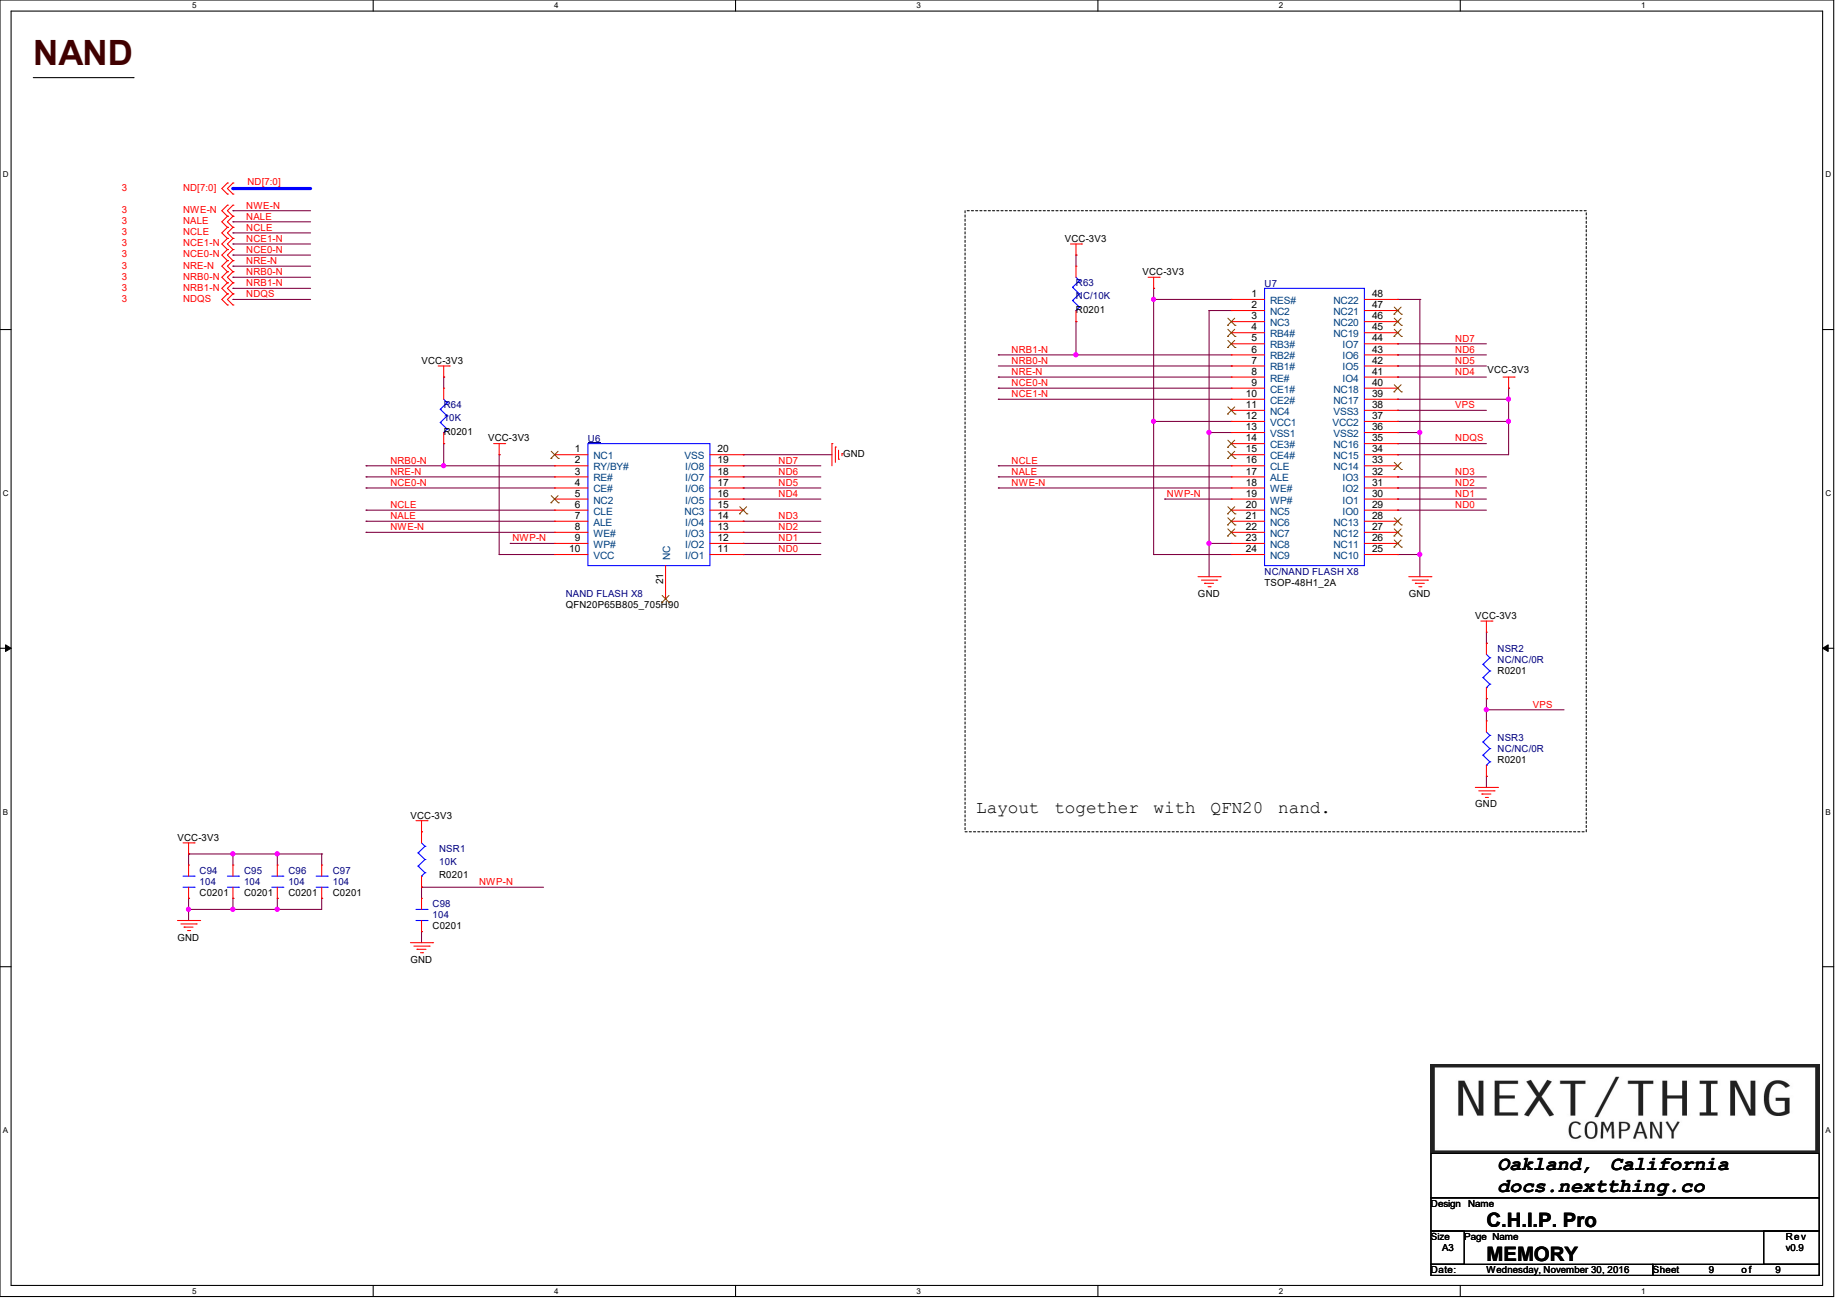
[picture p52: page 9]

R0201 NAND FLASH X8 U6 QFN20P65B805_705H90 CLE 6 ALE 7 RE# 3 VCC 10 CE# 4 NC2 5 WE# 8 WP# 9 NC1 1 RY/BY# 2

Layout together with QFN20 nand. NWP-N
