ntc-chip-revived/CHIP_Pro-Hardware/v0.9/CHIP_Pro_v0_9_Stackup.pdf

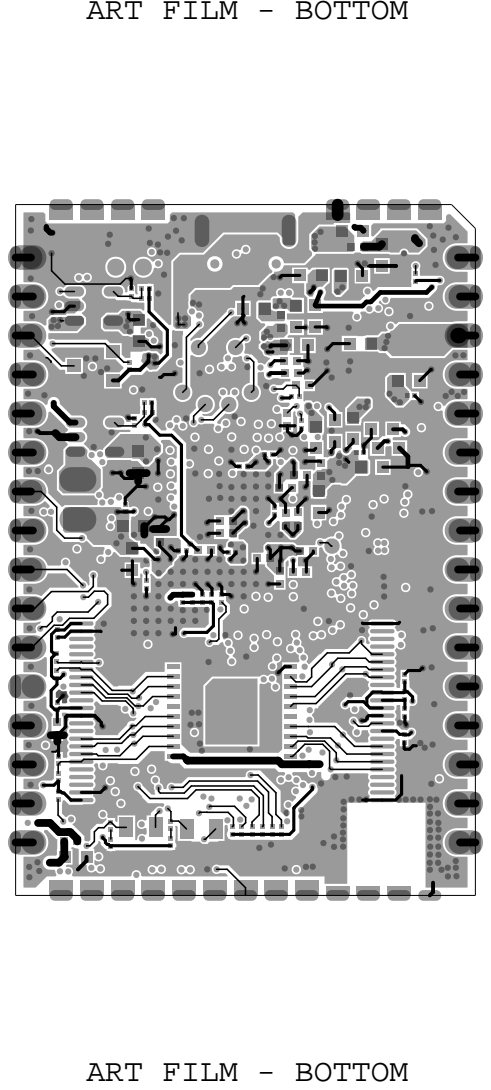
[picture p53: page 1]

ART FILM - BOTTOM

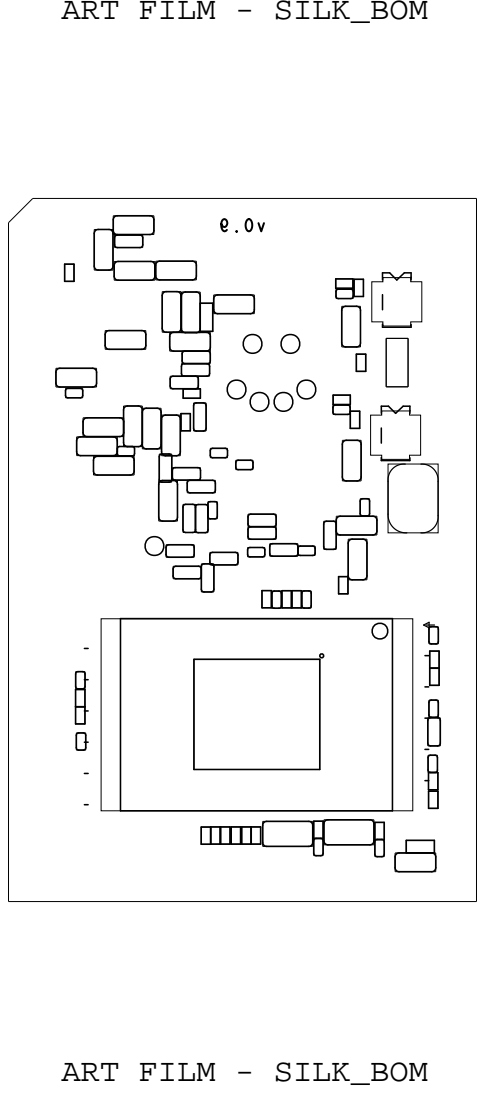
[picture p54: page 2]
ART FILM - SILK_BOM

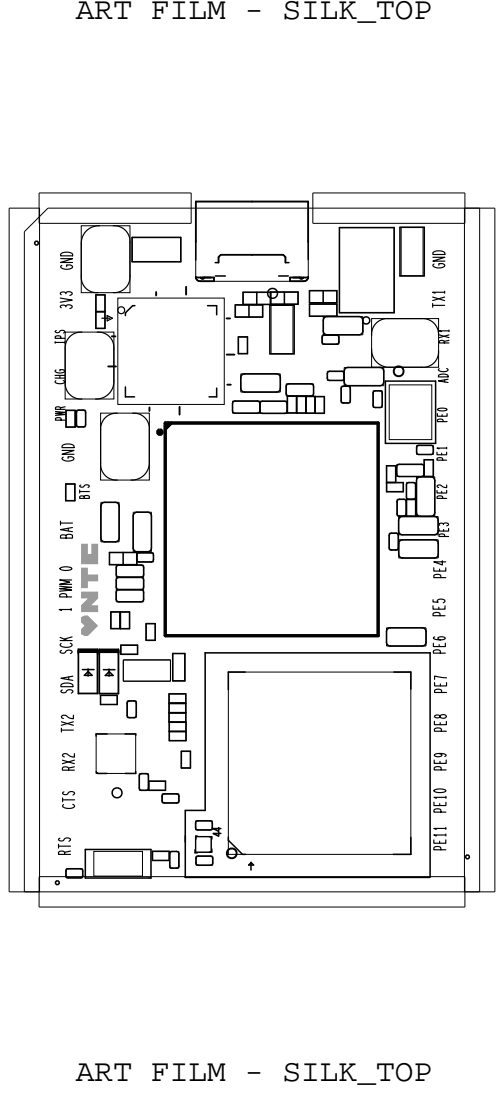
[picture p55: page 3]
ART FILM - SILK_TOP; GND TX1 ADC RX1 PE0 PE2 PE1 PE3 PE5 PE4 PE7 PE6 PE8 PE10 PE9 PE11; BTS

GND 3V3 CHG IPS PWR

GND 0 BAT 1 PWM SCK SDA TX2 CTS RX2 RTS

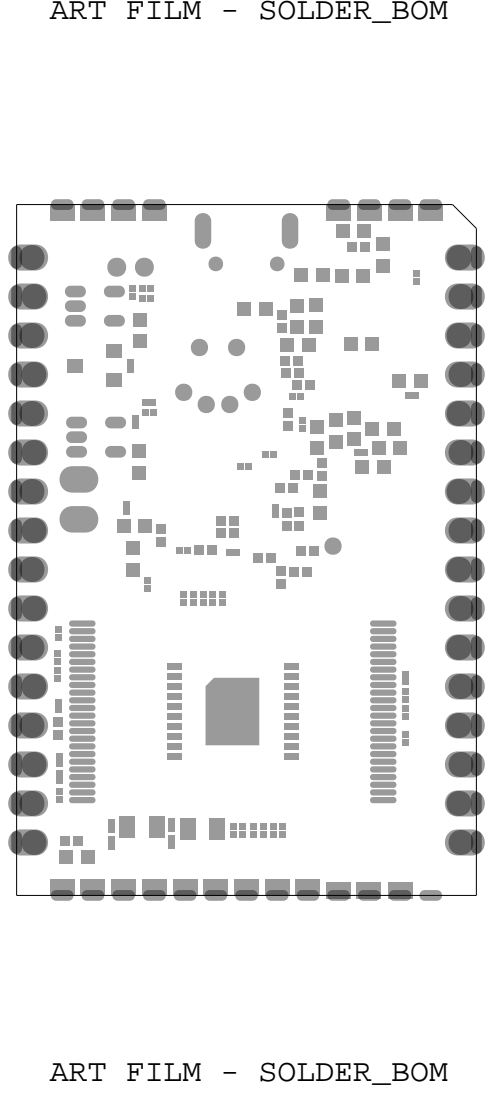
[picture p56: page 4]
ART FILM - SOLDER_BOM

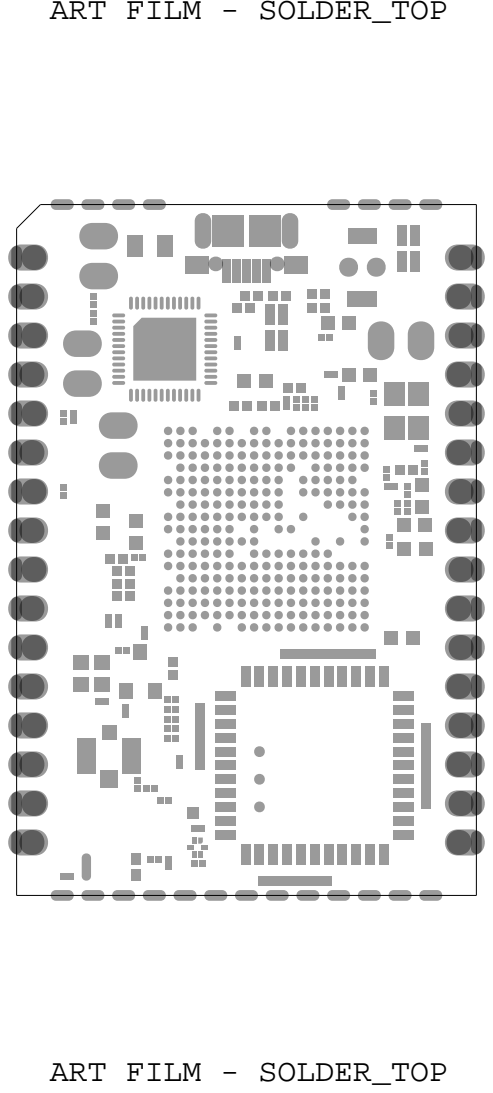
[picture p57: page 5]
ART FILM - SOLDER_TOP

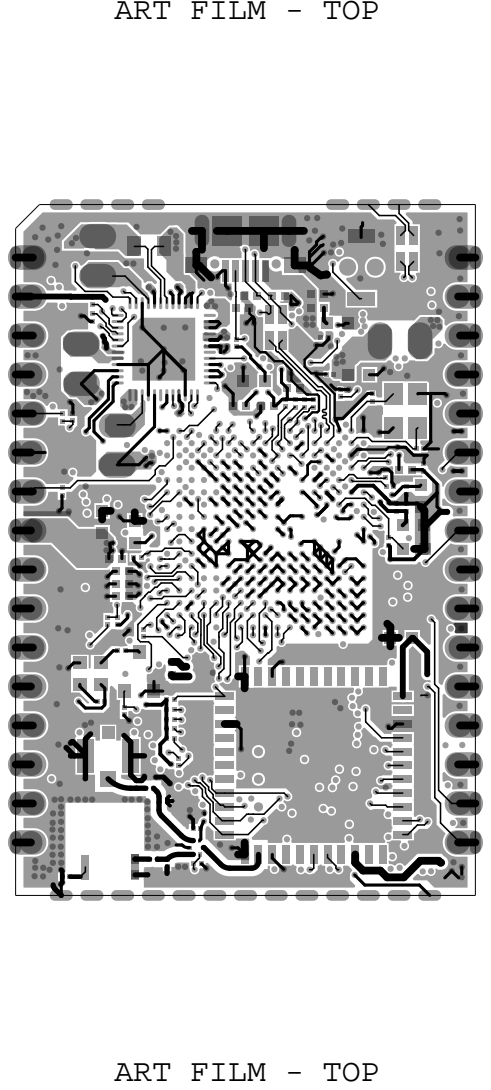
[picture p58: page 6]

ART FILM - TOP

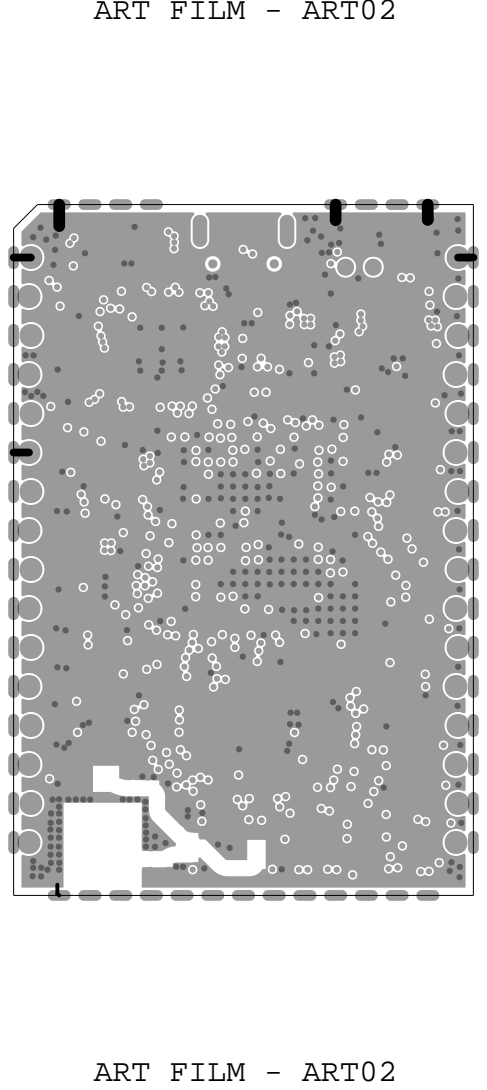
[picture p59: page 7]
ART FILM - ART02

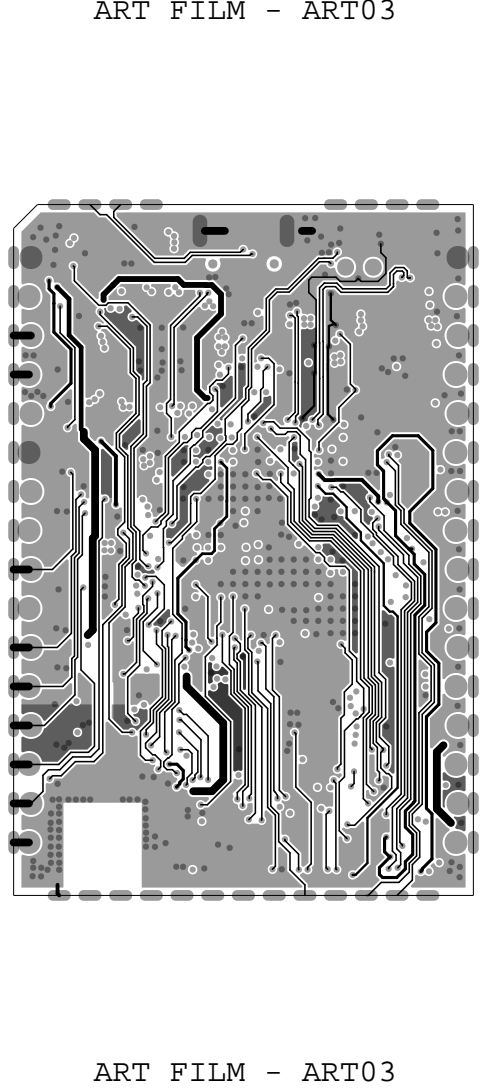
[picture p60: page 8]
ART FILM - ART03

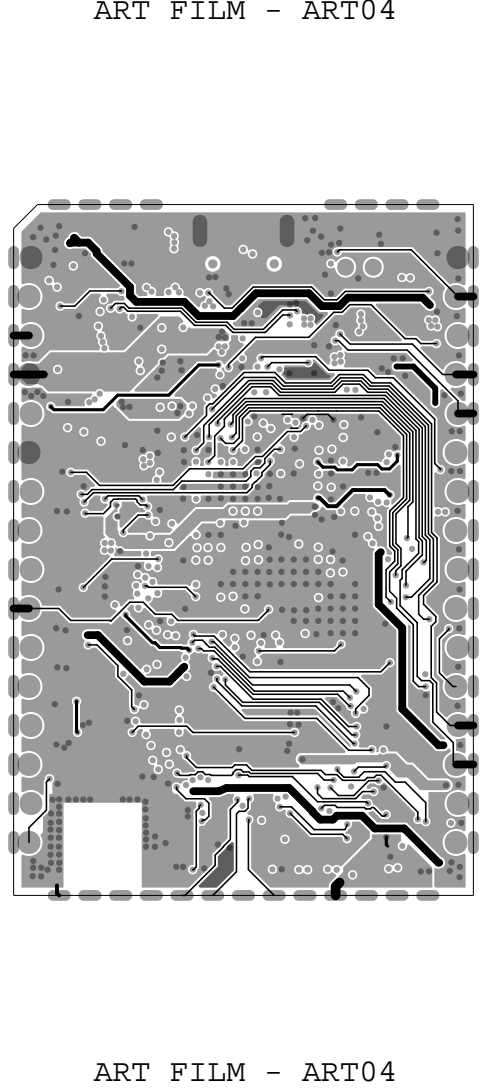
[picture p61: page 9]
ART FILM - ART04

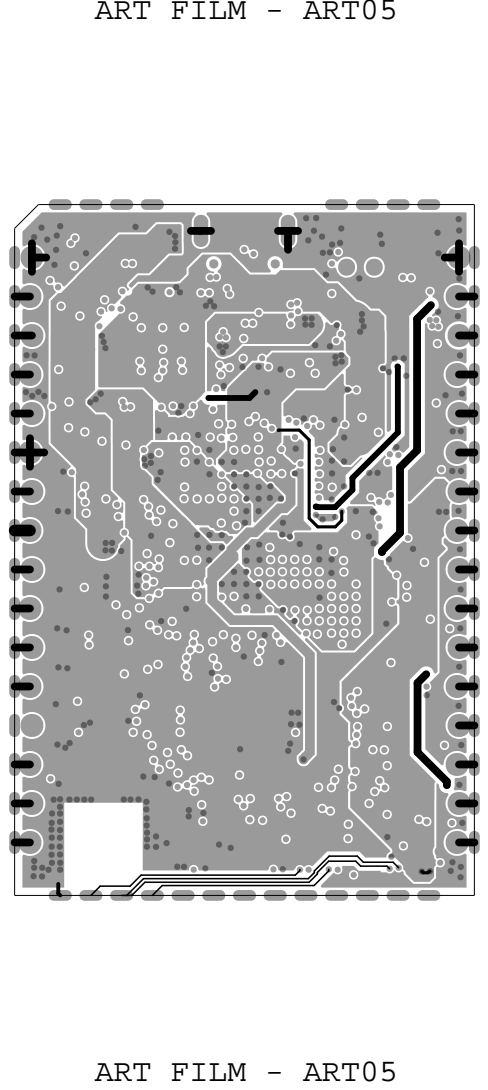
[picture p62: page 10]
ART FILM - ART05

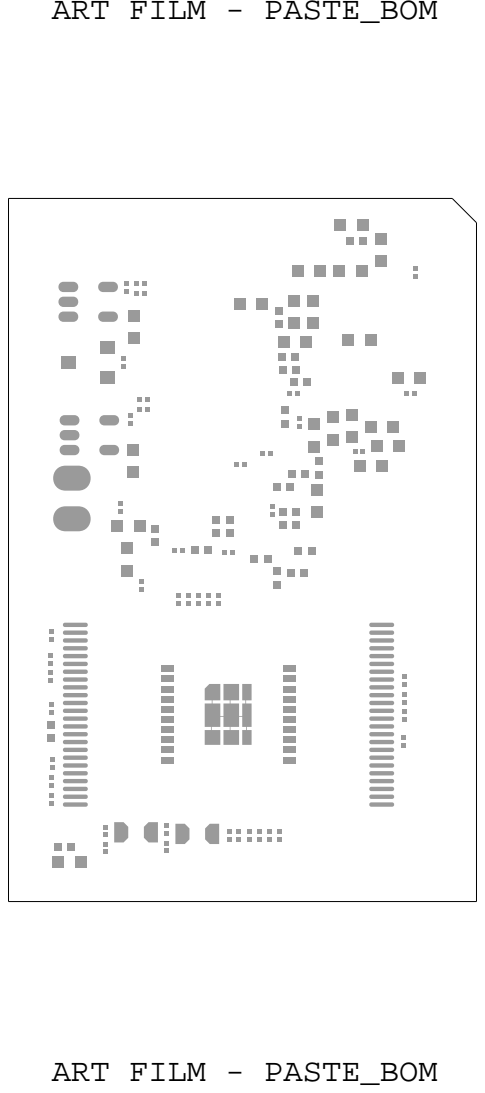
[picture p63: page 11]
ART FILM - PASTE_BOM

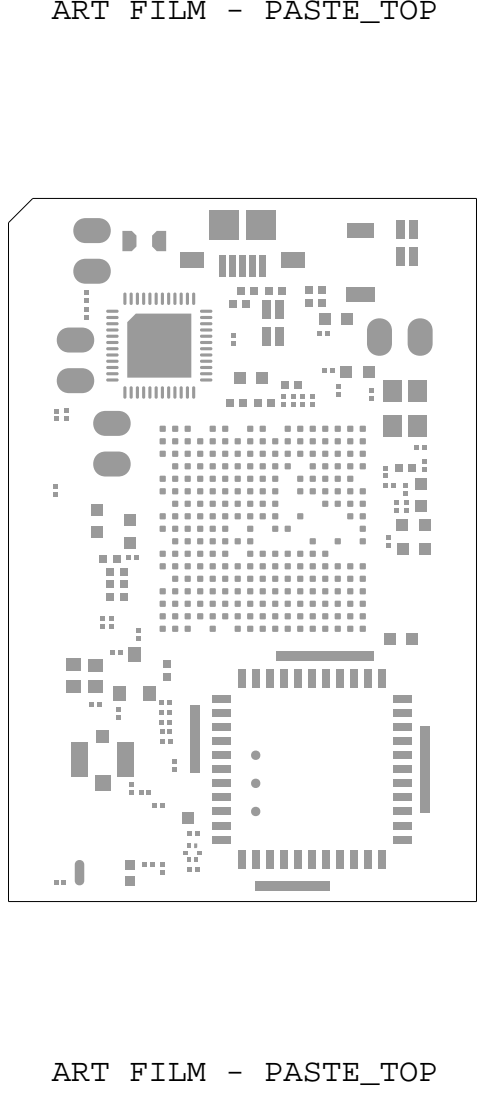
[picture p64: page 12]
ART FILM - PASTE_TOP
