ntc-chip-revived/CHIP_Pro-Hardware/v0.9/CHIP_Pro_v0_9_PartMap.pdf

# ART FILM - ST

J4 | J6

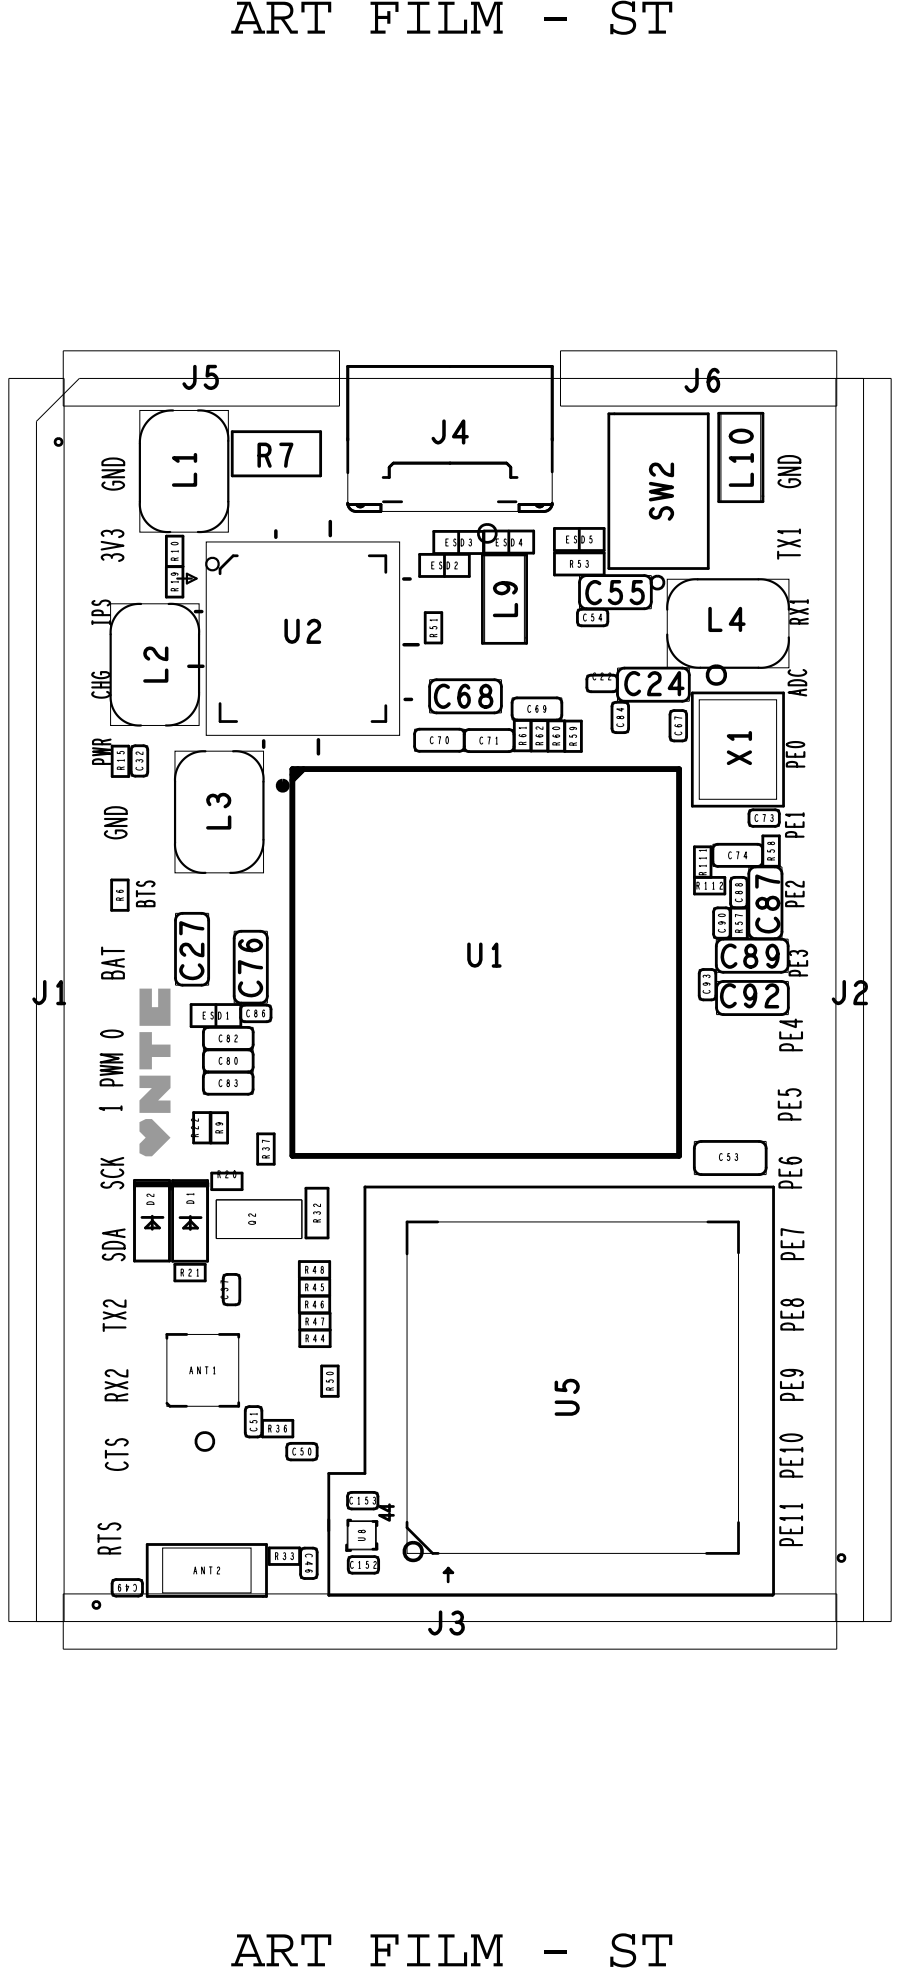
[picture p65: page 1]

# ART FILM - SB

v0.9

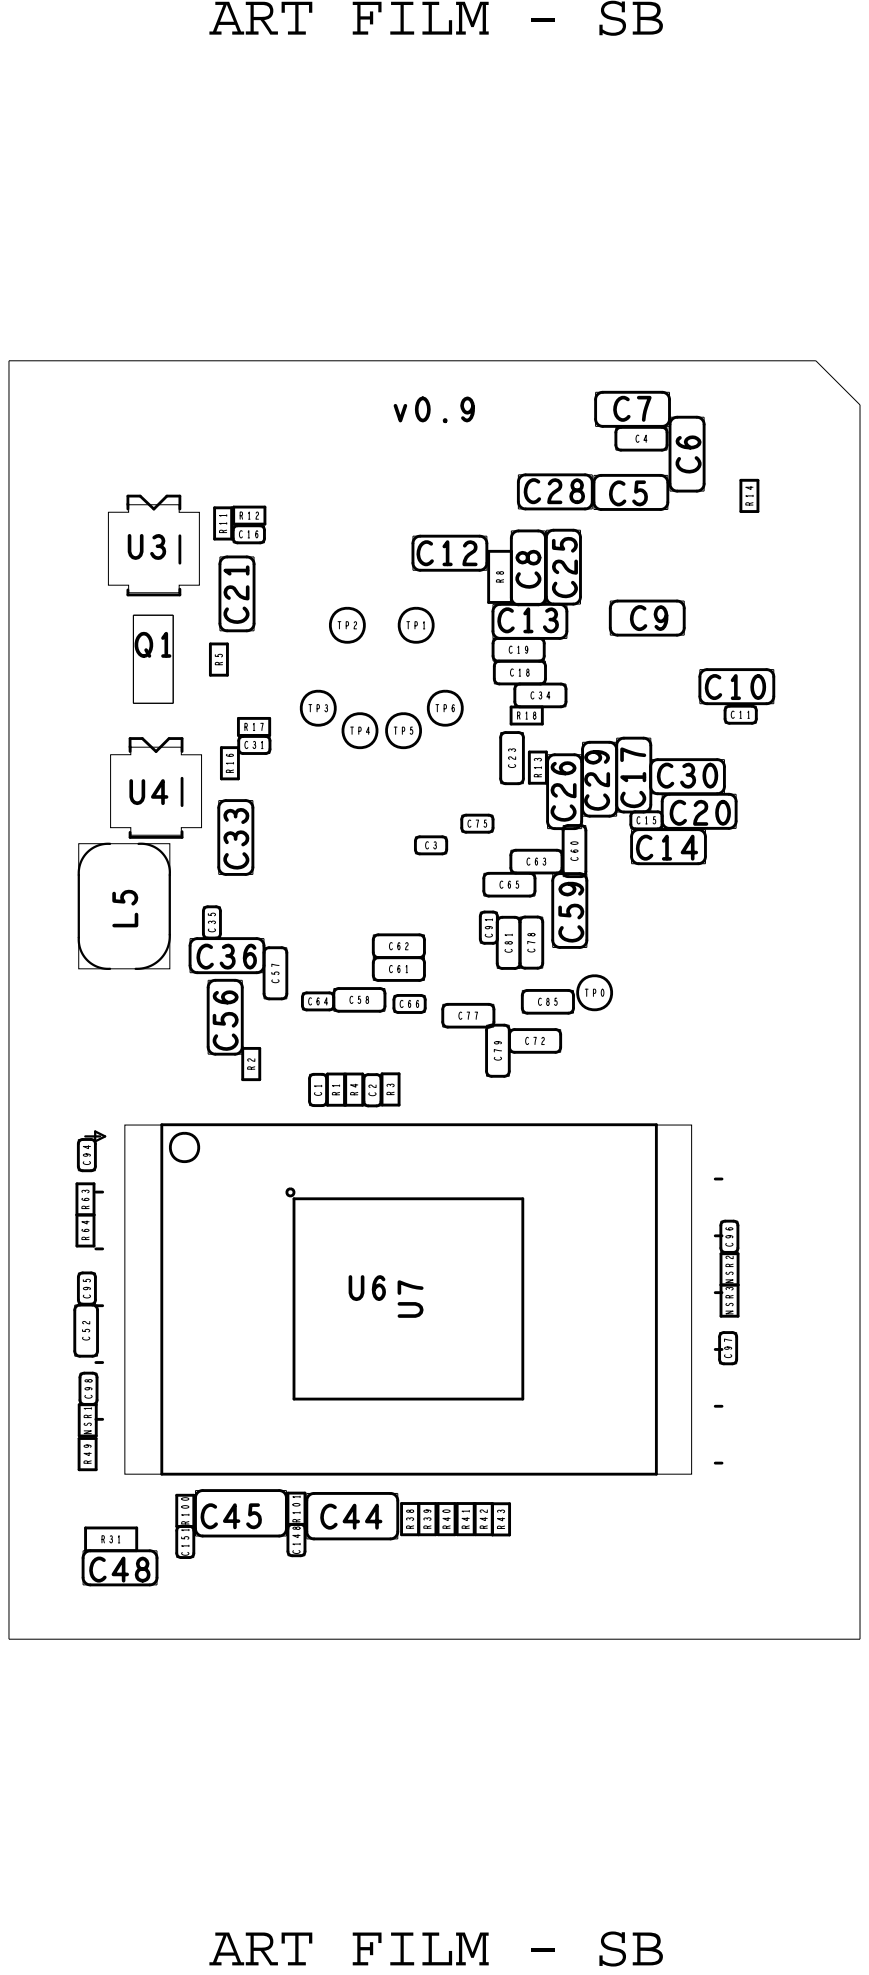
[picture p66: page 2]
